roblatour/ESP32TimeServer/main/main.cpp

// ESP32 Time Server v3.0.4
// Copyright Rob Latour, 2026
// License: MIT
// Website: https://github.com/roblatour/ESP32TimeServer
//
// ESP32 Dev Board:     ESP32-P4-ETH https://www.waveshare.com/esp32-p4-eth.htm
//                                   https://www.waveshare.com/wiki/ESP32-P4-ETH?srsltid=AfmBOoo6nZm5hsPAhtpzT6lWSHd2zhWNPM_mqgbNvyoESbjvbO7uykcH
//
//                      NOTE: Powering a Waveshare ESP32-P4 POE development board by either a USB C cable or
//                      via POE Ethernet cable is sufficient to power this project,
//
//                      *****************************************************************************************************
//                      * HOWEVER DO NOT POWER THE DEVELOPMENT BOARD VIA BOTH ITS USB C CONNECTION AND POE AT THE SAME TIME *
//                      *****************************************************************************************************
//
// GNSS (recommended):  SparkFun GNSS Receiver Breakout - MAX-M10S  https://www.sparkfun.com/sparkfun-gnss-receiver-breakout-max-m10s-qwiic.html
//
// LCD2004:             blue/green screen with HD44780 I2C serial interface adapter https://www.aliexpress.com/item/1005006829045609.html.
//
// Wiring:
//
// (mandatory) GNSS module wiring to and from the ESP32-P4-ETH board:
// GNSS GND            <- -> ESP32-P4-ETH GND
// GNSS VCC            <- -> ESP32-P4-ETH 3V3
// GNSS TXD            <- -> ESP32-P4-ETH GPIO17 (RX)
// GNSS RXD            <- -> ESP32-P4-ETH GPIO16 (TX)
// GNSS PPS            <- -> ESP32-P4-ETH GPIO18
//
// (optional) LCD204A V1.5 (HD44780 + PCF8574T I2C backpack) wiring to and from the ESP32-P4-ETH board:
// LCD GND            <- -> ESP32-P4-ETH GND
// LCD VCC            <- -> ESP32-P4-ETH 3V3
// LCD SDA            <- -> ESP32-P4-ETH GPIO8 (SDA)
// LCD SLC/SCL        <- -> ESP32-P4-ETH GPIO7 (SCL)
//
// (optional) Uptime momentary button to and from teh ESP32-P4-ETH board:
// one terminal       <- -> ESP32-P4-ETH GPI03
// the other terminal <- -> ESP32-P4-ETH GND

#include <atomic>
#include <cerrno>
#include <cstdarg>
#include <cstdio>
#include <cstdlib>
#include <cstring>
#include <ctime>
#include <dirent.h>
#include <sys/stat.h>
#include <sys/time.h>
#include <unistd.h>
#include <algorithm>
#include <string>
#include <vector>

#include "Arduino.h"
#include "ArduinoOTA.h"
#include "ETH.h"
#include "SparkFun_u-blox_GNSS_v3.h"
#include "ESP32TimeServerSettings.h"
#include "custom/app_metadata.h"
#if SYMMETRIC_KEY_AUTHENTICATION_ENABLED
#include "custom/ntp_auth.h"
#endif
#include "custom/ntp_cache.h"

extern "C"
{
#include "esp_chip_info.h"
#include "esp_event.h"
#include "esp_eth_clock.h"
#include "esp_eth_driver.h"
#include "esp_eth_mac_esp.h"
#include "esp_log.h"
#include "ff.h"
#include "esp_mac.h"
#if MQTT_ENABLED
#include "esp_heap_caps.h"
#include "mqtt_client.h"
#endif
#include "esp_netif.h"
#include "esp_rom_sys.h"
#include "esp_timer.h"
#include "esp_vfs_fat.h"
#include "nvs.h"
#include "driver/mcpwm_cap.h"
#if RBG_LED_KY_016_MODULE_ENABLED
#include "driver/ledc.h"
#endif
#if RBG_LED_WS2812_MODULE_ENABLED
#include "led_strip.h"
#endif
#include "driver/sdmmc_host.h"
#include "sd_pwr_ctrl_by_on_chip_ldo.h"
#include "sdmmc_cmd.h"
#include "nvs_flash.h"
#include "driver/gpio.h"
#include "freertos/FreeRTOS.h"
#include "freertos/event_groups.h"
#include "freertos/queue.h"
#include "freertos/semphr.h"
#include "freertos/task.h"
#if LIQUID_CRYSTAL_DISPLAY_ENABLED
#include "hd44780.h"
#include "pcf8574.h"
#endif
#include "lwip/inet.h"
#include "lwip/sockets.h"
}

static const char *TAG = "main_cpp";

// the following is used to determine the NTP load shedding threshold based on the ESP32-P4 chip version
static constexpr uint32_t NTP_Requests_Per_Second_Load_Shedding_Threshold_ESP32P4_ChipVersion1_3 = 8500;
static constexpr uint32_t NTP_Requests_Per_Second_Load_Shedding_Threshold_ESP32P4_ChipVersion_above_1_3 = 14500;
static uint32_t NTP_Requests_Per_Second_Load_Shedding_Threshold = 0;

// Optional startup health test
//
// When enabled the startup health test will perform a series of checks to ensure the system is functioning correctly at boot.
//
// These tests include:
//
// Part 1: the program sends itself NTPv3 and NTPv4 (standard and interleaved ) requests via IPv4 and IPv6,
// using loop back and assigned addresses,
//
// Part 2: it health test the same logic that all NTP requests go through to receive those requests,
// process and reply to them using standard and RFC 9769-compatible interleaved  responses,
//
// Part 3: it verifying the responses to ensure proper operations and reports a pass/fail result.
//
// Additionally, this activity is reflected in regular receive/send/client stats within MQTT reporting. .
//
// The startup health test can be useful during development and troubleshooting, but it slightly increase boot time
// and resource usage.
//
// However, it is recommended to keep this option be disabled in production builds to minimize boot time and resource usage.
// Also, and perhaps more importantly, as its results may be misinterpreted.
// For example: if the user's network does not support IPv6 the IPv6 tests may fail even though the system is
// functioning correctly.
//
// Here is what a successful startup health test looks like in the logs:
/*


I (39724) main_cpp: Health Check started
I (39725) main_cpp: Health Check 01 - IPv4 loopback: NTPv3 standard      - Passed
I (39725) main_cpp: Health Check 02 - IPv4 loopback: NTPv4 standard      - Passed
I (39731) main_cpp: Health Check 03 - IPv4 loopback: NTPv4 interleaved   - Passed
I (39739) main_cpp: Health Check 04 - IPv4 loopback: NTPv4 auth standard - Passed
I (39746) main_cpp: Health Check 05 - IPv4 loopback: NTPv4 auth interlv  - Passed
I (39753) main_cpp: Health Check 06 - IPv4 loopback: NTPv4 invalid auth  - Passed
I (39760) main_cpp: Health Check 07 - IPv4 loopback: NTPv4 unknown key   - Passed
I (39767) main_cpp: Health Check 08 - IPv4 loopback: NTPv4 truncated MAC - Passed
I (39775) main_cpp: Health Check 09 - IPv4 loopback: NTPv4 altered reply - Passed
I (39782) main_cpp: Health Check 10 - IPv4 assigned: NTPv3 standard      - Passed
I (39789) main_cpp: Health Check 11 - IPv4 assigned: NTPv4 standard      - Passed
I (39796) main_cpp: Health Check 12 - IPv4 assigned: NTPv4 interleaved   - Passed
I (39803) main_cpp: Health Check 13 - IPv4 assigned: NTPv4 auth standard - Passed
I (39811) main_cpp: Health Check 14 - IPv4 assigned: NTPv4 auth interlv  - Passed
I (39818) main_cpp: Health Check 15 - IPv4 assigned: NTPv4 invalid auth  - Passed
I (39825) main_cpp: Health Check 16 - IPv4 assigned: NTPv4 unknown key   - Passed
I (39832) main_cpp: Health Check 17 - IPv4 assigned: NTPv4 truncated MAC - Passed
I (39839) main_cpp: Health Check 18 - IPv4 assigned: NTPv4 altered reply - Passed
I (39847) main_cpp: Health Check 19 - IPv6 loopback: NTPv3 standard      - Passed
I (39854) main_cpp: Health Check 20 - IPv6 loopback: NTPv4 standard      - Passed
I (39861) main_cpp: Health Check 21 - IPv6 loopback: NTPv4 interleaved   - Passed
I (39868) main_cpp: Health Check 22 - IPv6 loopback: NTPv4 auth standard - Passed
I (39876) main_cpp: Health Check 23 - IPv6 loopback: NTPv4 auth interlv  - Passed
I (39883) main_cpp: Health Check 24 - IPv6 loopback: NTPv4 invalid auth  - Passed
I (39890) main_cpp: Health Check 25 - IPv6 loopback: NTPv4 unknown key   - Passed
I (39897) main_cpp: Health Check 26 - IPv6 loopback: NTPv4 truncated MAC - Passed
I (39904) main_cpp: Health Check 27 - IPv6 loopback: NTPv4 altered reply - Passed
I (39912) main_cpp: Health Check 28 - IPv6 assigned: NTPv3 standard      - Passed
I (39919) main_cpp: Health Check 29 - IPv6 assigned: NTPv4 standard      - Passed
I (39926) main_cpp: Health Check 30 - IPv6 assigned: NTPv4 interleaved   - Passed
I (39933) main_cpp: Health Check 31 - IPv6 assigned: NTPv4 auth standard - Passed
I (39940) main_cpp: Health Check 32 - IPv6 assigned: NTPv4 auth interlv  - Passed
I (39948) main_cpp: Health Check 33 - IPv6 assigned: NTPv4 invalid auth  - Passed
I (39955) main_cpp: Health Check 34 - IPv6 assigned: NTPv4 unknown key   - Passed
I (39962) main_cpp: Health Check 35 - IPv6 assigned: NTPv4 truncated MAC - Passed
I (39969) main_cpp: Health Check 36 - IPv6 assigned: NTPv4 altered reply - Passed
I (39976) main_cpp: Health Check 37 - MQTT metrics                       - Passed
I (39984) main_cpp: Health Check completed

Most of the health checks have fairly obvious purposes based on their names, but a couple of them,
truncated MAC and altered reply tests, may require more explanation (detailed below).

For truncated MAC:
This test sends an otherwise valid NTP packet but deliberately cuts off part of the authentication field (the Message Authentication Code)
before the server processes it. The server receives a packet whose header and timestamps look fine, but whose MAC is shorter than expected,
so when it tries to verify the MAC at the end of the packet, the check fails and the reply is rejected or flagged as invalid. In effect,
it’s testing that the server does not accept packets where the integrity/authentication data has been damaged or partially missing, even
though the rest of the packet structure appears normal.

For altered reply:
This test takes a valid NTP response and then modifies some of its contents—typically one or more timestamp fields or other critical header
values—after the server has generated it but before the client treats it as trustworthy. When the client compares the altered reply against
what it expects (e.g., matching originate/receive/transmit timestamps or internal state), the inconsistency causes the response to be rejected
or treated as an error rather than used to adjust time. By doing this, the test checks that the client detects tampering or corruption in the
reply and doesn’t blindly accept time data that has been changed in transit.

*/

#define STARTUP_HEALTH_TEST_ENABLED 0 // 0 = Disabled; 1 = Enabled

// The following conditional compile flag is used to determine the ideal stack sizes for
// xTaskCreatePinnedToCore calls used throughout the program.
//
// Unless you are changing the code associated with options below and need to know the impacts of
// those changes have on the stack sizes then the conditional compile flags below should be disabled

#define CALCULATE_STACK_SIZES_ENABLED 0 // 0 = Disabled; 1 = Enabled

// FreeRTOS task stack allocations, in bytes.

static constexpr size_t Ethernet_Transport_Recovery_Task_Stack_Size = 3072;
static constexpr size_t GNSS_Recovery_Task_Stack_Size = 12288;
static constexpr size_t GNSS_Time_Sync_Task_Stack_Size = 2517;
static constexpr size_t Hardware_NTP_Server_Task_Stack_Size = 4096;
static constexpr size_t LED_LCD_Button_Task_Stack_Size = 3217;
static constexpr size_t Ethernet_Setup_Task_Stack_Size = 4096;
static constexpr size_t MQTT_Service_Task_Stack_Size = 3512;
static constexpr size_t NTP_Cache_Purge_Task_Stack_Size = 2304;
static constexpr size_t NTP_Server_Task_Stack_Size = 3560;
static constexpr size_t OTE_Service_Task_Stack_Size = 3560; // unlikely to exceed this stack size (based on current implementation)
static constexpr size_t PPS_Discipline_Task_Stack_Size = 2390;

static constexpr unsigned int Default_Safety_Margin_Percent = 30; // unless otherwise specified add this percentage to the highest stack usage as a safety margin

#if CALCULATE_STACK_SIZES_ENABLED

// For the purposes of calculating stack sizes force DEBUG_ENABLED if any of the stack size calculations are enabled
// so that the task includes all debug processing is included in the stack size calculations
#define DEBUG_ENABLED 1

// For the purposes of calculating stack sizes force all MQTT tasks as enabled if MQTT_ENABLED is enabled
#if MQTT_ENABLED
#define MQTT_CLIENT_REPORTING_ENABLED 1
#define MQTT_MEMORY_REPORTING_ENABLED 1
#define MQTT_HISTORICAL_REPORTING_ENABLED 1
#endif

typedef enum
{
    Ethernet_Transport_Recovery,
    GNSS_Recovery,
    GNSS_Time_Sync,
    Hardware_NTP_Server,
    LED_LCD_Button,
    MQTT_Service,
    NTP_Cache_Purge,
    NTP_Server,
    OTE_Service,
    PPS_Discipline
} TaskToPinToCore_t;

static size_t Highest_Ethernet_Transport_Recovery_Task_Stack_Size = 0;
static size_t Highest_GNSS_Recovery_Task_Stack_Size = 0;
static size_t Highest_GNSS_Time_Sync_Task_Stack_Size = 0;
static size_t Highest_Hardware_NTP_Server_Task_Stack_Size = 0;
static size_t Highest_LED_LCD_Button_Task_Stack_Size = 0;
static size_t Highest_MQTT_Service_Task_Stack_Size = 0;
static size_t Highest_NTP_Cache_Purge_Task_Stack_Size = 0;
static size_t Highest_NTP_Server_Task_Stack_Size = 0;
static size_t Highest_OTE_Service_Task_Stack_Size = 0;
static size_t Highest_PPS_Discipline_Task_Stack_Size = 0;

static SemaphoreHandle_t s_task_stack_usage_mutex = nullptr;

static void report_current_task_stack_usage(TaskToPinToCore_t task_id)
{
    xSemaphoreTake(s_task_stack_usage_mutex, portMAX_DELAY);

    const char *task_name = nullptr;
    size_t allocated_bytes = 0;
    unsigned int safety_margin_percent = 30;
    bool highest_value_changed = false;
    bool show_details = false;

    switch (task_id)
    {
    case Ethernet_Transport_Recovery:
        task_name = "ethernet_transport_task";
        allocated_bytes = Ethernet_Transport_Recovery_Task_Stack_Size;
        break;
    case GNSS_Recovery:
        task_name = "gnss_recovery_task";
        allocated_bytes = GNSS_Recovery_Task_Stack_Size;
        break;
    case GNSS_Time_Sync:
        task_name = "gnss_time_sync_task";
        allocated_bytes = GNSS_Time_Sync_Task_Stack_Size;
        break;
    case Hardware_NTP_Server:
        task_name = "hardware_ntp_server_task";
        allocated_bytes = Hardware_NTP_Server_Task_Stack_Size;
        break;
    case LED_LCD_Button:
        task_name = "LED_LCD_Button_task";
        allocated_bytes = LED_LCD_Button_Task_Stack_Size;
        safety_margin_percent = 70;
        break;
    case MQTT_Service:
        task_name = "mqtt_service_task";
        allocated_bytes = MQTT_Service_Task_Stack_Size;
        break;
    case NTP_Cache_Purge:
        task_name = "ntp_cache_purge_task";
        allocated_bytes = NTP_Cache_Purge_Task_Stack_Size;
        break;
    case NTP_Server:
        task_name = "ntp_server_task";
        allocated_bytes = NTP_Server_Task_Stack_Size;
        safety_margin_percent = 50;
        break;
    case OTE_Service:
        task_name = "ote_service_task";
        allocated_bytes = OTE_Service_Task_Stack_Size;
        break;
    case PPS_Discipline:
        task_name = "pps_discipline_task";
        allocated_bytes = PPS_Discipline_Task_Stack_Size;
        break;
    default:
        task_name = "unknown_task";
        break;
    }

    // calculate the suggested stack size based on the peak usage and safety margin

    const size_t high_watermark_bytes = uxTaskGetStackHighWaterMark(nullptr);
    const size_t peak_usage_bytes = allocated_bytes > high_watermark_bytes ? allocated_bytes - high_watermark_bytes : 0;
    const size_t curent_suggestion = (peak_usage_bytes * (100U + safety_margin_percent) + 99U) / 100U;

    if (show_details)
    {
        ESP_LOGI(task_name,
                 "Stack report: Allocated=%u bytes, HighWater=%u bytes unused, PeakUsage=%u bytes, Suggested=%u bytes",
                 static_cast<unsigned int>(allocated_bytes),
                 static_cast<unsigned int>(high_watermark_bytes),
                 static_cast<unsigned int>(peak_usage_bytes),
                 static_cast<unsigned int>(curent_suggestion));
    }

    if (curent_suggestion == 0)
        ESP_LOGE(task_name, "Error: Suggested stack size is 0 bytes. Try increasing the allocted bytes of %u", static_cast<unsigned int>(allocated_bytes));

    switch (task_id)
    {
    case Ethernet_Transport_Recovery:
        if (curent_suggestion > Highest_Ethernet_Transport_Recovery_Task_Stack_Size)
        {
            Highest_Ethernet_Transport_Recovery_Task_Stack_Size = curent_suggestion;
            highest_value_changed = true;
        }
        break;
    case GNSS_Recovery:
        if (curent_suggestion > Highest_GNSS_Recovery_Task_Stack_Size)
        {
            Highest_GNSS_Recovery_Task_Stack_Size = curent_suggestion;
            highest_value_changed = true;
        }
        break;
    case GNSS_Time_Sync:
        if (curent_suggestion > Highest_GNSS_Time_Sync_Task_Stack_Size)
        {
            Highest_GNSS_Time_Sync_Task_Stack_Size = curent_suggestion;
            highest_value_changed = true;
        }
        break;
    case Hardware_NTP_Server:
        if (curent_suggestion > Highest_Hardware_NTP_Server_Task_Stack_Size)
        {
            Highest_Hardware_NTP_Server_Task_Stack_Size = curent_suggestion;
            highest_value_changed = true;
        }
        break;
    case LED_LCD_Button:
        if (curent_suggestion > Highest_LED_LCD_Button_Task_Stack_Size)
        {
            Highest_LED_LCD_Button_Task_Stack_Size = curent_suggestion;
            highest_value_changed = true;
        }
        break;
    case MQTT_Service:
        if (curent_suggestion > Highest_MQTT_Service_Task_Stack_Size)
        {
            Highest_MQTT_Service_Task_Stack_Size = curent_suggestion;
            highest_value_changed = true;
        }
        break;
    case NTP_Cache_Purge:
        if (curent_suggestion > Highest_NTP_Cache_Purge_Task_Stack_Size)
        {
            Highest_NTP_Cache_Purge_Task_Stack_Size = curent_suggestion;
            highest_value_changed = true;
        }
        break;
    case NTP_Server:
        if (curent_suggestion > Highest_NTP_Server_Task_Stack_Size)
        {
            Highest_NTP_Server_Task_Stack_Size = curent_suggestion;
            highest_value_changed = true;
        }
        break;
    case OTE_Service:
        if (curent_suggestion > Highest_OTE_Service_Task_Stack_Size)
        {
            Highest_OTE_Service_Task_Stack_Size = curent_suggestion;
            highest_value_changed = true;
        }

        break;
    case PPS_Discipline:
        if (curent_suggestion > Highest_PPS_Discipline_Task_Stack_Size)
        {
            Highest_PPS_Discipline_Task_Stack_Size = curent_suggestion;
            highest_value_changed = true;
        }
        break;
    default:

        break;
    }

    // Report the highest suggested stack sizes for all tasks to date in such a way that they can be easily copied into the code above
    // If no new highest value has yet been reported for a task the value shown will be 0, the old value will remain as the comment
    if (highest_value_changed)
    {
        ESP_LOGI(TAG, "Suggested updated task stack sizes:");
        ESP_LOGI(TAG, " ");

        if (Highest_Ethernet_Transport_Recovery_Task_Stack_Size > Ethernet_Transport_Recovery_Task_Stack_Size)
            ESP_LOGW(TAG, "static constexpr size_t Ethernet_Transport_Recovery_Task_Stack_Size = %u; // %u;", static_cast<unsigned int>(Highest_Ethernet_Transport_Recovery_Task_Stack_Size), static_cast<unsigned int>(Ethernet_Transport_Recovery_Task_Stack_Size));
        else
            ESP_LOGI(TAG, "static constexpr size_t Ethernet_Transport_Recovery_Task_Stack_Size = %u; // %u;", static_cast<unsigned int>(Highest_Ethernet_Transport_Recovery_Task_Stack_Size), static_cast<unsigned int>(Ethernet_Transport_Recovery_Task_Stack_Size));

        if (Highest_GNSS_Recovery_Task_Stack_Size > GNSS_Recovery_Task_Stack_Size)
            ESP_LOGW(TAG, "static constexpr size_t GNSS_Recovery_Task_Stack_Size = %u; // %u;", static_cast<unsigned int>(Highest_GNSS_Recovery_Task_Stack_Size), static_cast<unsigned int>(GNSS_Recovery_Task_Stack_Size));
        else
            ESP_LOGI(TAG, "static constexpr size_t GNSS_Recovery_Task_Stack_Size = %u; // %u;", static_cast<unsigned int>(Highest_GNSS_Recovery_Task_Stack_Size), static_cast<unsigned int>(GNSS_Recovery_Task_Stack_Size));

        if (Highest_GNSS_Time_Sync_Task_Stack_Size > GNSS_Time_Sync_Task_Stack_Size)
            ESP_LOGW(TAG, "static constexpr size_t GNSS_Time_Sync_Task_Stack_Size = %u; // %u;", static_cast<unsigned int>(Highest_GNSS_Time_Sync_Task_Stack_Size), static_cast<unsigned int>(GNSS_Time_Sync_Task_Stack_Size));
        else
            ESP_LOGI(TAG, "static constexpr size_t GNSS_Time_Sync_Task_Stack_Size = %u; // %u;", static_cast<unsigned int>(Highest_GNSS_Time_Sync_Task_Stack_Size), static_cast<unsigned int>(GNSS_Time_Sync_Task_Stack_Size));

        if (Highest_Hardware_NTP_Server_Task_Stack_Size > Hardware_NTP_Server_Task_Stack_Size)
            ESP_LOGW(TAG, "static constexpr size_t Hardware_NTP_Server_Task_Stack_Size = %u; // %u;", static_cast<unsigned int>(Highest_Hardware_NTP_Server_Task_Stack_Size), static_cast<unsigned int>(Hardware_NTP_Server_Task_Stack_Size));
        else
            ESP_LOGI(TAG, "static constexpr size_t Hardware_NTP_Server_Task_Stack_Size = %u; // %u;", static_cast<unsigned int>(Highest_Hardware_NTP_Server_Task_Stack_Size), static_cast<unsigned int>(Hardware_NTP_Server_Task_Stack_Size));

        if (Highest_LED_LCD_Button_Task_Stack_Size > LED_LCD_Button_Task_Stack_Size)
            ESP_LOGW(TAG, "static constexpr size_t LED_LCD_Button_Task_Stack_Size = %u; // %u;", static_cast<unsigned int>(Highest_LED_LCD_Button_Task_Stack_Size), static_cast<unsigned int>(LED_LCD_Button_Task_Stack_Size));
        else
            ESP_LOGI(TAG, "static constexpr size_t LED_LCD_Button_Task_Stack_Size = %u; // %u;", static_cast<unsigned int>(Highest_LED_LCD_Button_Task_Stack_Size), static_cast<unsigned int>(LED_LCD_Button_Task_Stack_Size));

        if (Highest_MQTT_Service_Task_Stack_Size > MQTT_Service_Task_Stack_Size)
            ESP_LOGW(TAG, "static constexpr size_t MQTT_Service_Task_Stack_Size = %u; // %u;", static_cast<unsigned int>(Highest_MQTT_Service_Task_Stack_Size), static_cast<unsigned int>(MQTT_Service_Task_Stack_Size));
        else
            ESP_LOGI(TAG, "static constexpr size_t MQTT_Service_Task_Stack_Size = %u; // %u;", static_cast<unsigned int>(Highest_MQTT_Service_Task_Stack_Size), static_cast<unsigned int>(MQTT_Service_Task_Stack_Size));

        if (Highest_NTP_Cache_Purge_Task_Stack_Size > NTP_Cache_Purge_Task_Stack_Size)
            ESP_LOGW(TAG, "static constexpr size_t NTP_Cache_Purge_Task_Stack_Size = %u; // %u;", static_cast<unsigned int>(Highest_NTP_Cache_Purge_Task_Stack_Size), static_cast<unsigned int>(NTP_Cache_Purge_Task_Stack_Size));
        else
            ESP_LOGI(TAG, "static constexpr size_t NTP_Cache_Purge_Task_Stack_Size = %u; // %u;", static_cast<unsigned int>(Highest_NTP_Cache_Purge_Task_Stack_Size), static_cast<unsigned int>(NTP_Cache_Purge_Task_Stack_Size));

        if (Highest_NTP_Server_Task_Stack_Size > NTP_Server_Task_Stack_Size)
            ESP_LOGW(TAG, "static constexpr size_t NTP_Server_Task_Stack_Size = %u; // %u;", static_cast<unsigned int>(Highest_NTP_Server_Task_Stack_Size), static_cast<unsigned int>(NTP_Server_Task_Stack_Size));
        else
            ESP_LOGI(TAG, "static constexpr size_t NTP_Server_Task_Stack_Size = %u; // %u;", static_cast<unsigned int>(Highest_NTP_Server_Task_Stack_Size), static_cast<unsigned int>(NTP_Server_Task_Stack_Size));

        if (Highest_OTE_Service_Task_Stack_Size > OTE_Service_Task_Stack_Size)
            ESP_LOGW(TAG, "static constexpr size_t OTE_Service_Task_Stack_Size = %u; // %u;", static_cast<unsigned int>(Highest_OTE_Service_Task_Stack_Size), static_cast<unsigned int>(OTE_Service_Task_Stack_Size));
        else
            ESP_LOGI(TAG, "static constexpr size_t OTE_Service_Task_Stack_Size = %u; // %u;", static_cast<unsigned int>(Highest_OTE_Service_Task_Stack_Size), static_cast<unsigned int>(OTE_Service_Task_Stack_Size));

        if (Highest_PPS_Discipline_Task_Stack_Size > PPS_Discipline_Task_Stack_Size)
            ESP_LOGW(TAG, "static constexpr size_t PPS_Discipline_Task_Stack_Size = %u; // %u;", static_cast<unsigned int>(Highest_PPS_Discipline_Task_Stack_Size), static_cast<unsigned int>(PPS_Discipline_Task_Stack_Size));
        else
            ESP_LOGI(TAG, "static constexpr size_t PPS_Discipline_Task_Stack_Size = %u; // %u;", static_cast<unsigned int>(Highest_PPS_Discipline_Task_Stack_Size), static_cast<unsigned int>(PPS_Discipline_Task_Stack_Size));

        ESP_LOGI(TAG, " ");
    };

    xSemaphoreGive(s_task_stack_usage_mutex);
}

#endif

#ifndef UBLOX_COMPLIANT_GNSS_RECEIVER_ENABLED
#define UBLOX_COMPLIANT_GNSS_RECEIVER_ENABLED 1
#endif

static constexpr gpio_num_t ETH_MDC_GPIO = GPIO_NUM_31;
static constexpr gpio_num_t ETH_MDIO_GPIO = GPIO_NUM_52;
static constexpr gpio_num_t ETH_PHY_RST_GPIO = GPIO_NUM_51;
static constexpr int ETH_PHY_ADDRESS = 1;

#if LIQUID_CRYSTAL_DISPLAY_ENABLED
static constexpr i2c_port_t LCD_I2C_PORT = I2C_NUM_0;
static constexpr gpio_num_t LCD_I2C_SDA_GPIO = GPIO_NUM_8;
static constexpr gpio_num_t LCD_I2C_SCL_GPIO = GPIO_NUM_7;
#endif

static constexpr uint16_t NTP_PORT = 123;
static constexpr size_t NTP_PACKET_SIZE = 48;
#if SYMMETRIC_KEY_AUTHENTICATION_ENABLED
static constexpr size_t NTP_MAX_PACKET_SIZE = NTP_PACKET_SIZE + NTP_AUTH_TRAILER_SIZE;
#else
static constexpr size_t NTP_MAX_PACKET_SIZE = NTP_PACKET_SIZE;
#endif
static constexpr uint64_t NTP_EPOCH_OFFSET = 2208988800ULL;
static constexpr int8_t NTP_PRECISION_EXPONENT = -13;
static constexpr uint32_t NTP_ROOT_DISPERSION = 66;
static constexpr uint64_t NTP_CACHE_TIMESTAMP_MATCH_TOLERANCE = 8;
static constexpr size_t NTP_SOCKET_BATCH_LIMIT = 16;
static constexpr EventBits_t ETH_CONNECTED_BIT = BIT0;
static constexpr EventBits_t ETH_GOT_IP_BIT = BIT1;
static constexpr EventBits_t ETH_GOT_IP6_BIT = BIT2;
static constexpr EventBits_t ETH_GOT_ROUTABLE_IP6_BIT = BIT3;
static constexpr size_t IP_ADDRESS_TEXT_SIZE = INET6_ADDRSTRLEN;
static constexpr uint32_t ROUTABLE_IPV6_ACQUISITION_TIMEOUT_MS = 30000;
static constexpr uint32_t OTE_Failure_Display_Time_Ms = 10000;
static constexpr uint32_t OTE_Reboot_Delay_Ms = 5000;

#if LIQUID_CRYSTAL_DISPLAY_ENABLED
static i2c_dev_t s_lcd_io{};
static uint8_t s_lcd_addr = 0;
static bool s_lcd_ready = false;
static hd44780_t s_lcd{};
static char s_lcd_last_lines[lcdRows][lcdColumns + 1] = {};
static bool s_lcd_line_cached[lcdRows] = {};
#else
#define display_line(...)
#endif

static std::string MACToBeUsed;

struct PpsCaptureEvent
{
    int64_t approximate_edge_us;
};

static constexpr uint32_t PPS_CAPTURE_RESOLUTION_HZ = 80000000;

static EventGroupHandle_t s_net_event_group = nullptr;
static SemaphoreHandle_t s_network_address_mutex = nullptr;
static SemaphoreHandle_t s_time_mutex = nullptr;
static SemaphoreHandle_t s_pps_semaphore = nullptr;
static QueueHandle_t s_pps_timestamp_queue = nullptr;
static QueueHandle_t s_pps_sync_timestamp_queue = nullptr;
static mcpwm_cap_timer_handle_t s_pps_capture_timer = nullptr;
static mcpwm_cap_channel_handle_t s_pps_capture_channel = nullptr;
static SemaphoreHandle_t s_ote_mutex = nullptr;
#if LIQUID_CRYSTAL_DISPLAY_ENABLED
static SemaphoreHandle_t s_lcd_mutex = nullptr;
#endif
static SemaphoreHandle_t s_sync_state_mutex = nullptr;

#if OTE_UPDATES_ENABLED
static bool s_ote_in_progress = false;
static bool s_ote_failed = false;
static bool s_ote_success = false;
static int s_ote_progress_percent = -1;
static int64_t s_ote_failure_display_until_us = 0;
static int64_t s_ote_reboot_at_us = 0;
static char s_ote_error_reason[lcdColumns + 1] = "";
#endif

static std::atomic<bool> s_safe_guard_tripped{false};
static std::atomic<bool> s_time_setting_in_progress{false};
static std::atomic<bool> s_time_has_been_set{false};
static std::atomic<uint64_t> s_ntp_reference_time_64{0};
static std::atomic<bool> s_ntp_reference_valid{false};
static std::atomic<bool> s_ptp_clock_ready{false};

static_assert(PreferIPvX == 0 || PreferIPvX == 1 || PreferIPvX == 2 || PreferIPvX == 4 || PreferIPvX == 6 || PreferIPvX == 8 || PreferIPvX == 9,
              "PreferIPvX must be 0, 1, 2, 4, 6, 8, or 9");

static char s_ip_address[IP_ADDRESS_TEXT_SIZE] = "";
static char s_ipv4_address[INET_ADDRSTRLEN] = "";
static char s_ipv6_address[IP_ADDRESS_TEXT_SIZE] = "";
enum class ipv6_address_priority_t : uint8_t
{
    none,
    link_local,
    unique_local,
    global_unicast
};
static ipv6_address_priority_t s_ipv6_address_priority = ipv6_address_priority_t::none;

struct network_address_snapshot_t
{
    char selected[IP_ADDRESS_TEXT_SIZE];
    char ipv4[INET_ADDRSTRLEN];
    char ipv6[IP_ADDRESS_TEXT_SIZE];
    ipv6_address_priority_t ipv6_priority;
};

static constexpr bool IPV4_ENABLED = PreferIPvX != 2;
static constexpr bool IPV6_ENABLED = PreferIPvX != 1;

static bool has_usable_network_address(EventBits_t event_bits)
{
    if (PreferIPvX == 1)
        return (event_bits & ETH_GOT_IP_BIT) != 0;
    if (PreferIPvX == 2)
        return (event_bits & ETH_GOT_ROUTABLE_IP6_BIT) != 0;
    return (event_bits & (ETH_GOT_IP_BIT | ETH_GOT_ROUTABLE_IP6_BIT)) != 0;
}

static void update_selected_ip_address_locked()
{
    const bool has_ipv4 = s_ipv4_address[0] != '\0';
    const bool has_ipv6 = s_ipv6_address[0] != '\0';

    const char *selected_address = "";
    if (PreferIPvX == 1)
        selected_address = s_ipv4_address;
    else if (PreferIPvX == 2)
        selected_address = s_ipv6_address;
    else if (PreferIPvX == 4)
        selected_address = has_ipv4 ? s_ipv4_address : s_ipv6_address;
    else if (PreferIPvX == 6)
        selected_address = has_ipv6 ? s_ipv6_address : s_ipv4_address;
    else if (strcmp(s_ip_address, s_ipv4_address) == 0 && has_ipv4)
        selected_address = s_ipv4_address;
    else if (strcmp(s_ip_address, s_ipv6_address) == 0 && has_ipv6)
        selected_address = s_ipv6_address;
    else
        selected_address = has_ipv4 ? s_ipv4_address : s_ipv6_address;

    snprintf(s_ip_address, sizeof(s_ip_address), "%s", selected_address);
}

static network_address_snapshot_t get_network_address_snapshot()
{
    network_address_snapshot_t snapshot{};
    if (s_network_address_mutex != nullptr && xSemaphoreTake(s_network_address_mutex, portMAX_DELAY) == pdTRUE)
    {
        snprintf(snapshot.selected, sizeof(snapshot.selected), "%s", s_ip_address);
        snprintf(snapshot.ipv4, sizeof(snapshot.ipv4), "%s", s_ipv4_address);
        snprintf(snapshot.ipv6, sizeof(snapshot.ipv6), "%s", s_ipv6_address);
        snapshot.ipv6_priority = s_ipv6_address_priority;
        xSemaphoreGive(s_network_address_mutex);
    }
    return snapshot;
}

static void clear_network_addresses()
{
    if (s_network_address_mutex == nullptr || xSemaphoreTake(s_network_address_mutex, portMAX_DELAY) != pdTRUE)
        return;

    s_ip_address[0] = '\0';
    s_ipv4_address[0] = '\0';
    s_ipv6_address[0] = '\0';
    s_ipv6_address_priority = ipv6_address_priority_t::none;
    xSemaphoreGive(s_network_address_mutex);
}

static void set_network_ipv4_address(const esp_ip4_addr_t &address)
{
    if (s_network_address_mutex == nullptr || xSemaphoreTake(s_network_address_mutex, portMAX_DELAY) != pdTRUE)
        return;

    snprintf(s_ipv4_address, sizeof(s_ipv4_address), IPSTR, IP2STR(&address));
    update_selected_ip_address_locked();
    xSemaphoreGive(s_network_address_mutex);
}

static void clear_network_ipv4_address()
{
    if (s_network_address_mutex == nullptr || xSemaphoreTake(s_network_address_mutex, portMAX_DELAY) != pdTRUE)
        return;

    s_ipv4_address[0] = '\0';
    update_selected_ip_address_locked();
    xSemaphoreGive(s_network_address_mutex);
}

static ipv6_address_priority_t get_ipv6_address_priority(const struct in6_addr &address)
{
    if ((address.s6_addr[0] & 0xE0) == 0x20)
        return ipv6_address_priority_t::global_unicast;
    if ((address.s6_addr[0] & 0xFE) == 0xFC)
        return ipv6_address_priority_t::unique_local;
    return ipv6_address_priority_t::link_local;
}

static bool set_network_ipv6_address(const esp_ip6_addr_t &address)
{
    struct in6_addr parsed_address{};
    memcpy(&parsed_address, address.addr, sizeof(parsed_address));
    const ipv6_address_priority_t priority = get_ipv6_address_priority(parsed_address);
    const bool is_routable = priority >= ipv6_address_priority_t::unique_local;

    char text_address[IP_ADDRESS_TEXT_SIZE] = "";
    if (inet_ntop(AF_INET6, &parsed_address, text_address, sizeof(text_address)) == nullptr)
        return false;

    if (s_network_address_mutex == nullptr || xSemaphoreTake(s_network_address_mutex, portMAX_DELAY) != pdTRUE)
        return false;

    if (priority >= s_ipv6_address_priority)
    {
        snprintf(s_ipv6_address, sizeof(s_ipv6_address), "%s", text_address);
        s_ipv6_address_priority = priority;
        update_selected_ip_address_locked();
    }
    xSemaphoreGive(s_network_address_mutex);
    return is_routable;
}

static void refresh_network_ipv6_addresses()
{
    if (!IPV6_ENABLED || ETH.netif() == nullptr)
        return;

    esp_ip6_addr_t addresses[CONFIG_LWIP_IPV6_NUM_ADDRESSES]{};
    const int address_count = esp_netif_get_all_ip6(ETH.netif(), addresses);
    bool routable_address_acquired = false;
    for (int index = 0; index < address_count; ++index)
        routable_address_acquired = set_network_ipv6_address(addresses[index]) || routable_address_acquired;

    if (address_count > 0)
        xEventGroupSetBits(s_net_event_group, ETH_GOT_IP6_BIT);
    if (routable_address_acquired)
        xEventGroupSetBits(s_net_event_group, ETH_GOT_ROUTABLE_IP6_BIT);
}

static void log_network_ipv6_addresses()
{
    if (!IPV6_ENABLED || ETH.netif() == nullptr)
        return;

    esp_ip6_addr_t addresses[CONFIG_LWIP_IPV6_NUM_ADDRESSES]{};
    const int address_count = esp_netif_get_all_ip6(ETH.netif(), addresses);
    if (address_count == 0)
    {
        ESP_LOGW(TAG, "Ethernet IPv6 candidates: none");
        return;
    }

    for (int index = 0; index < address_count; ++index)
    {
        struct in6_addr address{};
        memcpy(&address, addresses[index].addr, sizeof(address));
        char text_address[IP_ADDRESS_TEXT_SIZE] = "";
        if (inet_ntop(AF_INET6, &address, text_address, sizeof(text_address)) == nullptr)
            continue;

        const char *type = "link-local";
        switch (get_ipv6_address_priority(address))
        {
        case ipv6_address_priority_t::global_unicast:
            type = "global-unicast";
            break;
        case ipv6_address_priority_t::unique_local:
            type = "unique-local";
            break;
        default:
            break;
        }
        ESP_LOGI(TAG, "Ethernet IPv6 candidate: %s (%s)", text_address, type);
    }
}

static std::atomic<bool> s_ethernet_connected{false};
static std::atomic<bool> s_ipv4_ever_acquired{false};
static std::atomic<int64_t> s_last_physical_link_down_us{0};
static std::atomic<bool> s_ethernet_recovery_in_progress{false};
static std::atomic<bool> s_ethernet_recovery_rx_probe_active{false};
static std::atomic<uint32_t> s_ethernet_recovery_rx_probe_frames{0};
static std::atomic<bool> s_hardware_ntp_accepting{false};
static std::atomic<bool> s_ntp_external_responses_enabled{false};
static std::atomic<bool> s_ntp_server_ready{false};
#if RBG_LED_KY_016_MODULE_ENABLED || RBG_LED_WS2812_MODULE_ENABLED
static std::atomic<bool> s_gnss_pps_startup_qualification_in_progress{false};
static void control_RGB_LED(RGB_LED_Colour Colour, bool enabled);
#endif
#if RBG_LED_WS2812_MODULE_ENABLED
static led_strip_handle_t s_ws2812_strip = nullptr;
static uint8_t s_ws2812_brightness = 0;
#endif
static std::atomic<bool> s_open_for_business_message_written{false};
static std::atomic<int64_t> s_last_hardware_ntp_response_us{0};
static std::atomic<int64_t> s_last_ntp_input_us{0};
static std::atomic<int64_t> s_first_ntp_input_us{0};
static std::atomic<int64_t> s_last_ntp_response_us{0};
static std::atomic<int64_t> s_last_load_shedding_us{0};
static std::atomic<uint64_t> s_ntp_admission_window{0};
static std::atomic<uint32_t> s_ntp_input_count{0};
static std::atomic<bool> s_ntp_shed_during_period{false};
static SemaphoreHandle_t s_hardware_ntp_transmit_mutex = nullptr;

enum class ntp_transport_health_t : uint8_t
{
    link_down,
    no_ip,
    idle,
    healthy,
    stalled
};
static std::atomic<ntp_transport_health_t> s_ntp_transport_health{ntp_transport_health_t::idle};

static bool ntp_load_shedding_active()
{
    const int64_t last_shedding_us = s_last_load_shedding_us.load(std::memory_order_relaxed);
    return last_shedding_us > 0 && esp_timer_get_time() - last_shedding_us < 1500000LL;
}

static void record_ntp_input(int64_t now_us)
{
    s_ntp_input_count.fetch_add(1, std::memory_order_relaxed);
    s_last_ntp_input_us.store(now_us, std::memory_order_relaxed);
    int64_t first_input_us = 0;
    s_first_ntp_input_us.compare_exchange_strong(first_input_us, now_us, std::memory_order_relaxed);
}

static bool admit_ntp_request()
{
    const int64_t now_us = esp_timer_get_time();
    record_ntp_input(now_us);

    const uint32_t window = static_cast<uint32_t>(now_us / 100000LL);
    const uint32_t window_limit = NTP_Requests_Per_Second_Load_Shedding_Threshold / 10;
    uint64_t current = s_ntp_admission_window.load(std::memory_order_relaxed);
    for (;;)
    {
        const uint32_t current_window = static_cast<uint32_t>(current >> 32);
        const uint32_t active_window = current_window > window ? current_window : window;
        const uint32_t count = static_cast<uint32_t>(current);
        const uint32_t next_count = current_window == active_window ? count + 1 : 1;
        if (next_count > window_limit)
        {
            s_ntp_shed_during_period.store(true, std::memory_order_relaxed);
            s_last_load_shedding_us.store(now_us, std::memory_order_relaxed);
            return false;
        }
        const uint64_t next = (static_cast<uint64_t>(active_window) << 32) | next_count;
        if (s_ntp_admission_window.compare_exchange_weak(current, next, std::memory_order_relaxed))
            return true;
    }
}

static bool configure_static_ip();
static bool configure_hardware_timestamps();
static bool start_ethernet_driver();

static bool format_socket_address(const struct sockaddr_storage &address, char *buffer, size_t buffer_size)
{
    if (buffer_size == 0)
        return false;

    const void *source = nullptr;
    if (address.ss_family == AF_INET)
        source = &reinterpret_cast<const struct sockaddr_in *>(&address)->sin_addr;
    else if (address.ss_family == AF_INET6)
        source = &reinterpret_cast<const struct sockaddr_in6 *>(&address)->sin6_addr;
    else
    {
        buffer[0] = '\0';
        return false;
    }

    return inet_ntop(address.ss_family, source, buffer, buffer_size) != nullptr;
}

#if MQTT_ENABLED

static constexpr uint32_t MQTTFrequencyOfKeepAliveRequest = 30; // in seconds (do not raise above 30

// MQTT_MAX_REPORT_SIZE is based on MQTT_TF_Client_Limit (in ESP32TimeServerSetting.h)
// please see the spreadsheet at tools/json_message_calculator.xlsx for calculation details
// Note: increasing this limit will increase memory usage for MQTT report buffering and may impact system performance.
static constexpr size_t MQTT_MAX_REPORT_SIZE = 39166;

// MQTT_REPORT_SIZE based on MQTT_CLIENT_SIZE (below)
// please see the spreadsheet at tools/json_message_calculator.xlsx for calculation details
// Note: increasing this limit will increase memory usage for MQTT report buffering and may impact system performance.
static constexpr size_t MQTT_CLIENT_LIMIT = 50;
static constexpr size_t MQTT_REPORT_SIZE = 4966;

static constexpr size_t MQTT_NTP_EVENT_QUEUE_DEPTH = 1024;
static constexpr size_t MQTT_REPORT_QUEUE_DEPTH = 4;
static constexpr size_t MQTT_NTP_EVENT_BATCH_LIMIT = 128;

static constexpr uint32_t MQTT_RESTART_PUBLISH_TIMEOUT_MS = 1000;
static constexpr uint32_t MQTT_QUEUED_PUBLISH_DELAY_MS = 250;
static constexpr char TF_MOUNT_POINT[] = "/tfcard";
static constexpr char TF_QUEUE_DIRECTORY[] = "/tfcard/Queue";

struct mqtt_client_request_t
{
    sa_family_t address_family = AF_UNSPEC;
    uint8_t address[sizeof(struct in6_addr)] = {};
    uint32_t requests = 0;
};

struct mqtt_report_t
{
    char payload[MQTT_REPORT_SIZE] = "";
};

static SemaphoreHandle_t s_mqtt_stats_mutex = nullptr;
static QueueHandle_t s_mqtt_ntp_event_queue = nullptr;
static esp_mqtt_client_handle_t s_mqtt_client = nullptr;
static std::atomic<bool> s_mqtt_setup_failed{false};
static std::atomic<bool> s_mqtt_connected{false};
static std::atomic<bool> s_mqtt_has_connected{false};
static std::atomic<int64_t> s_mqtt_disconnected_since_us{0};
static std::atomic<int> s_mqtt_restart_publish_id{-1};
static std::atomic<bool> s_mqtt_restart_publish_completed{false};
static std::atomic<uint32_t> s_pps_pulses{0};
static std::atomic<uint32_t> s_ntp_requests_this_second{0};
static std::atomic<uint32_t> s_ntp_valid_requests{0};
static std::atomic<uint32_t> s_ntp_invalid_requests{0};
static std::atomic<uint32_t> s_ntp_authenticated_valid_requests{0};
static std::atomic<uint32_t> s_ntp_authenticated_invalid_requests{0};
static std::atomic<uint32_t> s_ntp_unauthenticated_valid_requests{0};
static std::atomic<uint32_t> s_ntp_unauthenticated_invalid_requests{0};
static std::atomic<uint32_t> s_ntp_responses{0};
static std::atomic<uint32_t> s_ntp_responses_synchronized_and_disciplined{0};
static std::atomic<uint32_t> s_ntp_responses_gnss_unsynchronized{0};
static std::atomic<uint32_t> s_ntp_responses_pps_undisciplined{0};
static std::atomic<uint32_t> s_ntp_telemetry_events_dropped{0};
static std::atomic<uint8_t> s_satellite_count{0};
static std::atomic<uint8_t> s_satellite_min{UINT8_MAX};
static std::atomic<uint8_t> s_satellite_max{0};

static void mqtt_note_satellite_count(uint8_t satellites)
{
    s_satellite_count.store(satellites, std::memory_order_relaxed);

    uint8_t minimum = s_satellite_min.load(std::memory_order_relaxed);
    while (satellites < minimum &&
           !s_satellite_min.compare_exchange_weak(minimum, satellites, std::memory_order_relaxed, std::memory_order_relaxed))
    {
    }

    uint8_t maximum = s_satellite_max.load(std::memory_order_relaxed);
    while (satellites > maximum &&
           !s_satellite_max.compare_exchange_weak(maximum, satellites, std::memory_order_relaxed, std::memory_order_relaxed))
    {
    }
}

static std::atomic<int64_t> s_eth_link_connected_us{0};
static std::atomic<int64_t> s_eth_link_up_total_us{0};
#if MQTT_ENABLED && MQTT_HISTORICAL_REPORTING_ENABLED
static std::atomic<time_t> s_last_synchronized_and_disciplined{0};
static std::atomic<time_t> s_last_gnss_unsynchronized{0};
static std::atomic<time_t> s_last_pps_undisciplined{0};
static std::atomic<bool> s_historical_gnss_fault_active{false};
static std::atomic<bool> s_historical_pps_fault_active{false};
#endif

#if MQTT_ENABLED && MQTT_CLIENT_REPORTING_ENABLED
static std::atomic<bool> s_mqtt_client_table_overflown{false};
static size_t s_mqtt_client_count = 0;
#endif

static int64_t s_mqtt_last_link_up_us = 0;
static mqtt_report_t s_mqtt_reports[MQTT_REPORT_QUEUE_DEPTH]{};
static char s_mqtt_payload[MQTT_MAX_REPORT_SIZE] = "";
static char s_mqtt_final_payload[MQTT_REPORT_SIZE] = "";
static size_t s_mqtt_report_head = 0;
static std::atomic<size_t> s_mqtt_queued_messages_count{0};
static uint32_t s_mqtt_queued_messages_discarded = 0;
static mqtt_client_request_t s_mqtt_clients[MQTT_TF_Client_Limit]{};
static std::atomic<bool> s_tf_queue_available{false};
static sdmmc_card_t *s_tf_card = nullptr;
static uint64_t s_tf_queue_next_sequence = 0;
static std::atomic<uint32_t> s_ntp_most_requests_per_second{0};
static char s_mqtt_uri[64] = "";
static char s_mqtt_report_topic[128] = "";
static char s_mqtt_status_topic[128] = "";

static void mqtt_publish_final_report();
static void mqtt_enqueue_ntp_request(const struct sockaddr_storage &source_address);
#endif

static void controlled_restart(const char *reason);

static HardwareSerial s_gnss_serial(1);
static SFE_UBLOX_GNSS_SERIAL s_gnss;
static uint32_t s_detected_gnss_baud = 0;
static std::atomic<bool> s_saved_gnss_baud_communication_failed{false};
static bool s_gnss_required_assume_success = false;

// The following flag for National Marine Electronics Association (NEMA) fallback doesn't determine if it is allowed or not
// rather the program sets it to true if it is required (due to an older / ubox noncompliant hardware gnss module being used)

static bool s_use_nmea_fallback = false;
static bool s_gnss_is_max_m10s = false;
static std::atomic<bool> s_gnss_locked{false};
static std::atomic<int64_t> s_gnss_lock_started_us{0};
static std::atomic<int64_t> s_gnss_locked_total_us{0};
static std::atomic<bool> s_pps_discipline_active{false};
static std::atomic<bool> s_gnss_recovery_in_progress{false};
static std::atomic<int64_t> s_last_gnss_recovery_us{0};

struct sync_faults_t
{
    bool pps_missing = false;
    bool gnss_invalid = false;
    bool sanity_mismatch = false;
    bool sync_stale = false;
};

static bool has_sync_fault(const sync_faults_t &faults)
{
    return faults.pps_missing || faults.gnss_invalid || faults.sanity_mismatch || faults.sync_stale;
}

struct sync_state_t
{
    int64_t last_successful_sync_us = 0;
    int64_t last_sync_attempt_us = 0;
    int64_t last_pps_seen_us = 0;
    time_t last_sync_delta_seconds = 0;
    uint32_t consecutive_sync_failures = 0;
    uint32_t consecutive_sanity_failures = 0;
    bool holdover_mode = false;
    bool pps_active = false;
    bool gnss_timing_valid = false;
    int64_t last_gnss_valid_us = 0;
    sync_faults_t faults{};
};

struct sync_candidate_t
{
    time_t candidate_time = 0;
    bool use_pps_alignment = false;
    bool used_nmea_fallback = false;
    int64_t pps_release_time_us = 0;
    sync_faults_t failures{};
};

static sync_state_t s_sync_state{};
static sync_state_t get_sync_state_snapshot();
static std::atomic<uint32_t> s_ntp_sync_state_sequence{0};
static std::atomic<int64_t> s_ntp_last_successful_sync_us{0};
static std::atomic<int64_t> s_ntp_last_gnss_valid_us{0};
static std::atomic<bool> s_ntp_pps_active{false};
static std::atomic<bool> s_ntp_gnss_timing_valid{false};
static std::atomic<bool> s_ntp_pps_missing{false};
static std::atomic<bool> s_ntp_gnss_invalid{false};
static std::atomic<bool> s_ntp_sanity_mismatch{false};
static std::atomic<bool> s_ntp_sync_stale{false};
static constexpr int64_t Sync_Stale_After_Us = static_cast<int64_t>(periodicGNSSRefreshEveryThisNumberOfMinutes) * 60LL * 1000000LL * 3LL;
static constexpr int64_t Gnss_Validity_Timeout_Us = 3500000LL;
static constexpr int64_t Sync_Reboot_After_Us = 30LL * 60LL * 1000000LL;
static constexpr int64_t Max_Sync_Attempt_Us = 10000000LL;
static constexpr int64_t Gnss_Invalid_Reacquisition_After_Us = 30LL * 1000000LL;
static constexpr int64_t Runtime_gnss_Recovery_Min_Interval_Us = 5LL * 60LL * 1000000LL;
static constexpr uint32_t Sync_Failures_Before_Runtime_Recovery = 20;
static constexpr uint32_t Sanity_Failures_Before_Fault = 2;
static constexpr uint32_t gnss_Startup_Qualification_Duration_Ms = 15000UL;
static constexpr uint32_t gnss_Startup_Qualification_PPS_Edges = 10;
static constexpr int64_t gnss_Startup_Min_PPS_Interval_Us = 800000LL;
static constexpr int64_t gnss_Startup_Max_PPS_Interval_Us = 1200000LL;

static constexpr char gnss_NVS_NAMESPACE[] = "gnss_state";
static constexpr char gnss_NVS_KEY_ID_TYPE[] = "id_type";
static constexpr char gnss_NVS_KEY_ID_VALUE[] = "id_value";
static constexpr char gnss_NVS_KEY_MAX_BAUD[] = "max_baud";
static constexpr char gnss_NVS_KEY_INITIAL_BAUD[] = "initial_baud";
static constexpr char gnss_NVS_KEY_ATTEMPT_NO_SIGNAL_RECOVERY[] = "no_sig_rcv";
static constexpr char restart_NVS_NAMESPACE[] = "restart_evt";
static constexpr char restart_NVS_KEY_PENDING[] = "pending";

static constexpr char gnss_ID_TYPE_UNIQID[] = "uniqid";
static constexpr char gnss_ID_TYPE_MODULE_FP[] = "module_fp";
static constexpr char gnss_ID_TYPE_GENERIC[] = "generic";
static constexpr char gnss_ID_VALUE_UNDETERMINED[] = "undetermined_gnss_board";

/* pre-release code - commented out
static constexpr bool reduceGNSSUART1OutputToTimeMessages = true;
static constexpr bool saveReducedGNSSUART1OutputPermanently = false;
*/
struct gnss_identity_t
{
    bool valid = false;
    char type[16] = "";
    char value[96] = "";
};

struct gnss_nvs_data_t
{
    bool has_stored_data = false;
    bool has_id_type = false;
    char id_type[16] = "";
    char id_value[96] = "";
    uint32_t initial_baud = 0;
    uint32_t max_baud = 0;
};

static uint32_t s_gnss_target_baud = 0;

struct nmea_rmc_time_t
{
    int year = 0;
    int month = 0;
    int day = 0;
    int hour = 0;
    int minute = 0;
    int second = 0;
};

static void refresh_sync_state_locked(sync_state_t *state, int64_t now_us)
{
    if (state == nullptr)
        return;

    bool sync_stale = state->last_successful_sync_us > 0 && (now_us - state->last_successful_sync_us) > Sync_Stale_After_Us;
    bool pps_missing = s_time_has_been_set.load() && !state->pps_active;
    bool gnss_missing = s_time_has_been_set.load() && (!state->gnss_timing_valid ||
                                                       state->last_gnss_valid_us == 0 ||
                                                       (now_us - state->last_gnss_valid_us) > Gnss_Validity_Timeout_Us);

    state->faults.sync_stale = sync_stale;
    state->faults.gnss_invalid = gnss_missing;
    state->faults.pps_missing = pps_missing;

#if DEBUG_ENABLED
    if (gnss_missing)
        ESP_LOGE(TAG, "GNSS invalid - GNSS missing.");
#endif

    state->holdover_mode = has_sync_fault(state->faults);
}

static void publish_ntp_sync_state_locked(const sync_state_t &state)
{
    s_ntp_sync_state_sequence.fetch_add(1, std::memory_order_release);
    s_ntp_last_successful_sync_us.store(state.last_successful_sync_us, std::memory_order_relaxed);
    s_ntp_last_gnss_valid_us.store(state.last_gnss_valid_us, std::memory_order_relaxed);
    s_ntp_pps_active.store(state.pps_active, std::memory_order_relaxed);
    s_ntp_gnss_timing_valid.store(state.gnss_timing_valid, std::memory_order_relaxed);
    s_ntp_pps_missing.store(state.faults.pps_missing, std::memory_order_relaxed);
    s_ntp_gnss_invalid.store(state.faults.gnss_invalid, std::memory_order_relaxed);
    s_ntp_sanity_mismatch.store(state.faults.sanity_mismatch, std::memory_order_relaxed);
    s_ntp_sync_stale.store(state.faults.sync_stale, std::memory_order_relaxed);
    s_ntp_sync_state_sequence.fetch_add(1, std::memory_order_release);
}

static void sync_state_note_attempt()
{
    if (xSemaphoreTake(s_sync_state_mutex, portMAX_DELAY) == pdTRUE)
    {
        s_sync_state.last_sync_attempt_us = esp_timer_get_time();
        refresh_sync_state_locked(&s_sync_state, s_sync_state.last_sync_attempt_us);
        publish_ntp_sync_state_locked(s_sync_state);
        xSemaphoreGive(s_sync_state_mutex);
    }
}

static void sync_state_note_pps_edge(int64_t edge_us)
{
    if (xSemaphoreTake(s_sync_state_mutex, portMAX_DELAY) == pdTRUE)
    {
        s_sync_state.last_pps_seen_us = edge_us;
        s_sync_state.pps_active = true;
        refresh_sync_state_locked(&s_sync_state, edge_us);
        publish_ntp_sync_state_locked(s_sync_state);
        xSemaphoreGive(s_sync_state_mutex);
    }
}

static void sync_state_note_pps_timeout(int64_t now_us)
{
#if MQTT_ENABLED && MQTT_HISTORICAL_REPORTING_ENABLED
    if (s_time_has_been_set.load() && !s_historical_pps_fault_active.exchange(true))
        s_last_pps_undisciplined.store(time(nullptr));
#endif

    if (xSemaphoreTake(s_sync_state_mutex, portMAX_DELAY) == pdTRUE)
    {
        s_sync_state.pps_active = false;
        refresh_sync_state_locked(&s_sync_state, now_us);
        publish_ntp_sync_state_locked(s_sync_state);
        xSemaphoreGive(s_sync_state_mutex);
    }
}

static void set_gnss_lock_state(bool valid)
{
    int64_t now_us = esp_timer_get_time();
    bool previous = s_gnss_locked.exchange(valid);
    if (previous == valid)
        return;

    if (valid)
    {
        s_gnss_lock_started_us.store(now_us);
    }
    else
    {
        int64_t lock_started_us = s_gnss_lock_started_us.exchange(0);
        if (lock_started_us > 0 && now_us > lock_started_us)
            s_gnss_locked_total_us.fetch_add(now_us - lock_started_us);
    }
}

static void sync_state_note_gnss_validity(bool valid)
{
    set_gnss_lock_state(valid);

#if MQTT_ENABLED && MQTT_HISTORICAL_REPORTING_ENABLED
    if (!valid && s_time_has_been_set.load() && !s_historical_gnss_fault_active.exchange(true))
        s_last_gnss_unsynchronized.store(time(nullptr));
#endif

    if (xSemaphoreTake(s_sync_state_mutex, portMAX_DELAY) == pdTRUE)
    {
        int64_t now_us = esp_timer_get_time();
        s_sync_state.gnss_timing_valid = valid;
        if (valid)
            s_sync_state.last_gnss_valid_us = now_us;
        refresh_sync_state_locked(&s_sync_state, now_us);
        publish_ntp_sync_state_locked(s_sync_state);
        xSemaphoreGive(s_sync_state_mutex);
    }
}

static uint32_t sync_state_note_failure(const sync_faults_t &faults, time_t update_delta)
{
    uint32_t failure_count = 0;

    if (faults.gnss_invalid)
        set_gnss_lock_state(false);

#if MQTT_ENABLED && MQTT_HISTORICAL_REPORTING_ENABLED
    if (s_time_has_been_set.load())
    {
        if (faults.gnss_invalid && !s_historical_gnss_fault_active.exchange(true))
            s_last_gnss_unsynchronized.store(time(nullptr));
        if (faults.pps_missing && !s_historical_pps_fault_active.exchange(true))
            s_last_pps_undisciplined.store(time(nullptr));
    }
#endif

    if (xSemaphoreTake(s_sync_state_mutex, portMAX_DELAY) == pdTRUE)
    {
        s_sync_state.last_sync_delta_seconds = update_delta;
        s_sync_state.consecutive_sync_failures++;
        s_sync_state.faults.pps_missing = s_sync_state.faults.pps_missing || faults.pps_missing;
        s_sync_state.faults.gnss_invalid = s_sync_state.faults.gnss_invalid || faults.gnss_invalid;
        s_sync_state.faults.sanity_mismatch = s_sync_state.faults.sanity_mismatch || faults.sanity_mismatch;
        s_sync_state.faults.sync_stale = s_sync_state.faults.sync_stale || faults.sync_stale;
        refresh_sync_state_locked(&s_sync_state, esp_timer_get_time());
        publish_ntp_sync_state_locked(s_sync_state);
        failure_count = s_sync_state.consecutive_sync_failures;
        xSemaphoreGive(s_sync_state_mutex);
    }

    return failure_count;
}

static uint32_t sync_state_note_sanity_retry(time_t update_delta)
{
    uint32_t failure_count = 0;

    if (xSemaphoreTake(s_sync_state_mutex, portMAX_DELAY) == pdTRUE)
    {
        s_sync_state.last_sync_delta_seconds = update_delta;
        s_sync_state.consecutive_sync_failures++;
        s_sync_state.consecutive_sanity_failures++;
        refresh_sync_state_locked(&s_sync_state, esp_timer_get_time());
        publish_ntp_sync_state_locked(s_sync_state);
        failure_count = s_sync_state.consecutive_sanity_failures;
        xSemaphoreGive(s_sync_state_mutex);
    }

    return failure_count;
}

static void sync_state_clear_sanity_failures()
{
    if (xSemaphoreTake(s_sync_state_mutex, portMAX_DELAY) == pdTRUE)
    {
        s_sync_state.consecutive_sanity_failures = 0;
        refresh_sync_state_locked(&s_sync_state, esp_timer_get_time());
        publish_ntp_sync_state_locked(s_sync_state);
        xSemaphoreGive(s_sync_state_mutex);
    }
}

static void sync_state_reset_failure_counters()
{
    if (xSemaphoreTake(s_sync_state_mutex, portMAX_DELAY) == pdTRUE)
    {
        s_sync_state.consecutive_sync_failures = 0;
        s_sync_state.consecutive_sanity_failures = 0;
        refresh_sync_state_locked(&s_sync_state, esp_timer_get_time());
        publish_ntp_sync_state_locked(s_sync_state);
        xSemaphoreGive(s_sync_state_mutex);
    }
}

static void sync_state_note_success(time_t update_delta)
{
    set_gnss_lock_state(true);

#if MQTT_ENABLED && MQTT_HISTORICAL_REPORTING_ENABLED
    bool recovery_completed = s_historical_gnss_fault_active.exchange(false) ||
                              s_historical_pps_fault_active.exchange(false);
    if (s_last_synchronized_and_disciplined.load() == 0 || recovery_completed)
        s_last_synchronized_and_disciplined.store(time(nullptr));
#endif

    if (xSemaphoreTake(s_sync_state_mutex, portMAX_DELAY) == pdTRUE)
    {
        s_sync_state.last_successful_sync_us = esp_timer_get_time();
        s_sync_state.gnss_timing_valid = true;
        s_sync_state.last_gnss_valid_us = s_sync_state.last_successful_sync_us;
        s_sync_state.last_sync_delta_seconds = update_delta;
        s_sync_state.consecutive_sync_failures = 0;
        s_sync_state.consecutive_sanity_failures = 0;
        s_sync_state.faults = {};
        refresh_sync_state_locked(&s_sync_state, s_sync_state.last_successful_sync_us);
        publish_ntp_sync_state_locked(s_sync_state);
        xSemaphoreGive(s_sync_state_mutex);
    }
}

static sync_state_t get_sync_state_snapshot()
{
    sync_state_t snapshot{};

    if (xSemaphoreTake(s_sync_state_mutex, portMAX_DELAY) == pdTRUE)
    {
        refresh_sync_state_locked(&s_sync_state, esp_timer_get_time());
        publish_ntp_sync_state_locked(s_sync_state);
        snapshot = s_sync_state;
        xSemaphoreGive(s_sync_state_mutex);
    }

    return snapshot;
}

static bool first_sync_candidates_are_plausible(const sync_candidate_t &first_candidate, const sync_candidate_t &second_candidate)
{
    time_t delta = second_candidate.candidate_time - first_candidate.candidate_time;
    return delta >= 1 && delta <= 3;
}

#if LIQUID_CRYSTAL_DISPLAY_ENABLED
static esp_err_t lcd_write_i2c(const hd44780_t *lcd, uint8_t data)
{
    (void)lcd;
    return pcf8574_port_write(&s_lcd_io, data);
}

static void init_lcd_descriptor()
{
    memset(&s_lcd, 0, sizeof(s_lcd));
    s_lcd.write_cb = lcd_write_i2c;
    s_lcd.font = HD44780_FONT_5X8;
    s_lcd.lines = lcdRows;
    s_lcd.pins.rs = 0;
    s_lcd.pins.e = 2;
    s_lcd.pins.d4 = 4;
    s_lcd.pins.d5 = 5;
    s_lcd.pins.d6 = 6;
    s_lcd.pins.d7 = 7;
    s_lcd.pins.bl = 3;
    s_lcd.backlight = true;
}

static void display_line(uint8_t row, const char *text)
{

    // LCD rows once displayed are cached and only updated when changed

    char padded[lcdColumns + 1];
    memset(padded, ' ', sizeof(padded) - 1);
    padded[lcdColumns] = '\0';

    if (text != nullptr)
    {
        size_t len = strlen(text);
        if (len > lcdColumns)
        {
            len = lcdColumns;
        }
        memcpy(padded, text, len);
    }

    if (!s_lcd_ready)
    {
#if DEBUG_ENABLED
        ESP_LOGW(TAG, "LCD not ready for row %u", row);
#endif
        return;
    }

    if (s_lcd_mutex != nullptr)
        xSemaphoreTake(s_lcd_mutex, portMAX_DELAY);

    if (row < lcdRows && s_lcd_line_cached[row] && strcmp(s_lcd_last_lines[row], padded) == 0)
    {
        if (s_lcd_mutex != nullptr)
            xSemaphoreGive(s_lcd_mutex);
        return;
    }

    esp_err_t err = hd44780_gotoxy(&s_lcd, 0, row);
    if (err != ESP_OK)
    {
#if DEBUG_ENABLED
        ESP_LOGE(TAG, "hd44780_gotoxy failed: %s", esp_err_to_name(err));
#endif
        if (s_lcd_mutex != nullptr)
            xSemaphoreGive(s_lcd_mutex);
        return;
    }

    err = hd44780_puts(&s_lcd, padded);
    if (err != ESP_OK)
    {
#if DEBUG_ENABLED
        ESP_LOGE(TAG, "hd44780_puts failed: %s", esp_err_to_name(err));
#endif
    }
    else if (row < lcdRows)
    {
        memcpy(s_lcd_last_lines[row], padded, sizeof(s_lcd_last_lines[row]));
        s_lcd_line_cached[row] = true;
    }

    if (s_lcd_mutex != nullptr)
        xSemaphoreGive(s_lcd_mutex);
}

static esp_err_t lcd_try_device_address(uint8_t address)
{
    uint8_t port_state = 0;

    memset(&s_lcd_io, 0, sizeof(s_lcd_io));
    esp_err_t err = pcf8574_init_desc(&s_lcd_io, address, LCD_I2C_PORT, LCD_I2C_SDA_GPIO, LCD_I2C_SCL_GPIO);
    if (err != ESP_OK)
        return err;

    err = pcf8574_port_read(&s_lcd_io, &port_state);
    if (err != ESP_OK)
    {
        pcf8574_free_desc(&s_lcd_io);
        memset(&s_lcd_io, 0, sizeof(s_lcd_io));
        return err;
    }

    s_lcd_addr = address;
    return ESP_OK;
}

static esp_err_t setup_lcd()
{
    init_lcd_descriptor();

    esp_err_t err = i2cdev_init();
    if (err != ESP_OK)
        return err;

    err = lcd_try_device_address(lcdI2CAddressPrimary);
    if (err != ESP_OK)
        err = lcd_try_device_address(lcdI2CAddressSecondary);

    if (err != ESP_OK)
        return err;

    err = hd44780_init(&s_lcd);
    if (err != ESP_OK)
        return err;

    err = hd44780_switch_backlight(&s_lcd, true);
    if (err != ESP_OK)
        return err;

    err = hd44780_control(&s_lcd, true, false, false);
    if (err != ESP_OK)
        return err;

    err = hd44780_clear(&s_lcd);
    if (err != ESP_OK)
        return err;

    s_lcd_ready = true;
    return ESP_OK;
}
#endif

static void display_selected_ip_address(int seconds)
{
    if (PreferIPvX == 9)
    {
        display_line(3, "");
        return;
    }

    static char last_known_IPv6_addresss[IP_ADDRESS_TEXT_SIZE] = "";

    static char ipv6_part1[IP_ADDRESS_TEXT_SIZE] = "";
    static char ipv6_part2[IP_ADDRESS_TEXT_SIZE] = "";

    network_address_snapshot_t addresses = get_network_address_snapshot();

    if (PreferIPvX == 8)
    {
        const char *ipv6_status = "N/A";
        if (addresses.ipv6[0] != '\0')
        {
            switch (addresses.ipv6_priority)
            {
            case ipv6_address_priority_t::global_unicast:
                ipv6_status = "GUA";
                break;
            case ipv6_address_priority_t::unique_local:
                ipv6_status = "ULA";
                break;
            case ipv6_address_priority_t::link_local:
                ipv6_status = "LLA";
                break;
            default:
                break;
            }
        }
        char status_line[lcdColumns + 1];
        snprintf(status_line, sizeof(status_line), "IPv4: %s  IPv6: %s", addresses.ipv4[0] != '\0' ? "OK" : "N/A", ipv6_status);
        display_line(3, status_line);
        return;
    }

    // if no IP address is selected, clear the display line
    if (addresses.selected[0] == '\0')
    {
        display_line(3, "");
        return;
    }

    // An IPv6 can change from Link-Local Address (LLA) to Unique-Local Address (ULA) to Global-Unicast Address (GUA)
    // so if the selected IPv6 address has changed reset the IPv6 address parts
    if (PreferIPvX == 0 || PreferIPvX == 2 || PreferIPvX == 6)
    {
        if (strcmp(addresses.ipv6, last_known_IPv6_addresss) != 0)
        {
            size_t total_len = strlen(addresses.ipv6);
            if (total_len == 0)
            {
                ipv6_part1[0] = '\0';
                ipv6_part2[0] = '\0';
                last_known_IPv6_addresss[0] = '\0';
            }
            else
            {
                size_t half_len = total_len / 2;
                while (half_len > 0 && addresses.ipv6[half_len] != ':')
                    half_len--;

                size_t remainder_len = total_len - half_len;
                strncpy(ipv6_part1, addresses.ipv6, half_len);
                ipv6_part1[half_len] = '\0';
                strncpy(ipv6_part2, addresses.ipv6 + half_len, remainder_len);
                ipv6_part2[remainder_len] = '\0';

                strncpy(last_known_IPv6_addresss, addresses.ipv6, IP_ADDRESS_TEXT_SIZE - 1);
                last_known_IPv6_addresss[IP_ADDRESS_TEXT_SIZE - 1] = '\0';
            }
        }
    }

    switch (PreferIPvX)
    {
    case 0:

        // no preference between IPv4 and IPv6
        // each minute:
        // display the IPv4 address for the first 20 seconds
        // display the first part of the IPv6 address in next 20 seconds
        // display the second part of the IPv6 address in the last 20 seconds

        if (seconds < 20)
            display_line(3, addresses.ipv4);
        else if (seconds < 40)
            display_line(3, ipv6_part1);
        else
            display_line(3, ipv6_part2);

        break;

    case 1:
    case 4:
        // Show the IPv4 address only
        if (strcmp(addresses.selected, addresses.ipv4) == 0)
        {
            display_line(3, addresses.selected);
            return;
        }
        break;

    case 2:
    case 6:
        // Show the IPv6 address only

        // each minute:
        // display the first part of the IPv6 address for the first 30 seconds
        // display the second part of the IPv6 address for the next 30 seconds
        if (seconds < 30)
            display_line(3, ipv6_part1);
        else
            display_line(3, ipv6_part2);
        break;
    }
}

static void apply_timezone_settings()
{
    setenv("TZ", timeZoneSpec, 1);
    tzset();
}

static void format_local_date_time(time_t utc_time, char *date_string, size_t date_size, char *time_string, size_t time_size)
{
    struct tm local_tm{};
    localtime_r(&utc_time, &local_tm);

    snprintf(date_string, date_size, "%04d-%02d-%02d", local_tm.tm_year + 1900, local_tm.tm_mon + 1, local_tm.tm_mday);

    int hour_value = local_tm.tm_hour;
    if (!display24HourFormat)
    {
        hour_value %= 12;
        if (hour_value == 0)
            hour_value = 12;
    }

    char zone[8] = "";

    if (displayTimeZone)
        strftime(zone, sizeof(zone), "%Z", &local_tm);

    const char *hour_format = displayHoursWithPaddedZero ? "%02d:%02d:%02d" : "%d:%02d:%02d";
    int len = snprintf(time_string, time_size, hour_format, hour_value, local_tm.tm_min, local_tm.tm_sec);

    if (!display24HourFormat && len >= 0 && static_cast<size_t>(len) < time_size)
        len += snprintf(time_string + len, time_size - len, " %s", local_tm.tm_hour < 12 ? "AM" : "PM");

    if (displayTimeZone && zone[0] != '\0' && len >= 0 && static_cast<size_t>(len) < time_size)
        snprintf(time_string + len, time_size - len, " %s", zone);
}

#if UPTIME_RESTART_BUTTON_ENABLED
static void get_uptime(char *buffer, size_t buffer_size)
{
    uint64_t total_seconds = static_cast<uint64_t>(esp_timer_get_time() / 1000000ULL);
    uint64_t days = total_seconds / 86400ULL;
    total_seconds %= 86400ULL;
    uint64_t hours = total_seconds / 3600ULL;
    total_seconds %= 3600ULL;
    uint64_t minutes = total_seconds / 60ULL;
    uint64_t seconds = total_seconds % 60ULL;
    snprintf(buffer, buffer_size, "%llu %02llu:%02llu:%02llu", days, hours, minutes, seconds);
}
#endif

static bool initialize_nvs_storage()
{
    esp_err_t err = nvs_flash_init();
    if (err == ESP_ERR_NVS_NO_FREE_PAGES || err == ESP_ERR_NVS_NEW_VERSION_FOUND)
    {
        ESP_LOGE(TAG, "NVS recovery requires operator action; automatic erase is disabled to preserve authentication storage");
        return false;
    }

    if (err != ESP_OK)
    {
#if DEBUG_ENABLED
        ESP_LOGE(TAG, "nvs_flash_init failed: %s", esp_err_to_name(err));
#endif
        return false;
    }

    return true;
}

static bool parse_mac_id_string(const char *text, uint8_t mac[6])
{
    if (text == nullptr || mac == nullptr || text[0] == '\0' || std::strlen(text) != 17)
        return false;

    if (text[2] != ':' || text[5] != ':' || text[8] != ':' || text[11] != ':' || text[14] != ':')
        return false;

    unsigned int values[6] = {};
    if (std::sscanf(text,
                    "%2x:%2x:%2x:%2x:%2x:%2x",
                    &values[0],
                    &values[1],
                    &values[2],
                    &values[3],
                    &values[4],
                    &values[5]) != 6)
        return false;

    for (size_t index = 0; index < 6; ++index)
        mac[index] = static_cast<uint8_t>(values[index]);

    return true;
}

static uint32_t get_highest_candidate_gnss_baud()
{
    return 921600;
}

static void build_candidate_baud_rates(std::vector<uint32_t> &out)
{
    static constexpr uint32_t all_candidate_baud_rates[] = {4800, 9600, 19200, 38400, 57600, 115200, 230400, 460800, 921600};

    out.assign(std::begin(all_candidate_baud_rates), std::end(all_candidate_baud_rates));
}

static bool load_gnss_nvs_data(gnss_nvs_data_t *data)
{
    if (data == nullptr)
        return false;

    *data = gnss_nvs_data_t{};

    nvs_handle_t handle = 0;
    esp_err_t err = nvs_open(gnss_NVS_NAMESPACE, NVS_READONLY, &handle);
    if (err == ESP_ERR_NVS_NOT_FOUND)
        return true;
    if (err != ESP_OK)
        return false;

    bool has_id_type_key = false;
    size_t type_length = 0;
    err = nvs_get_str(handle, gnss_NVS_KEY_ID_TYPE, nullptr, &type_length);
    if (err == ESP_OK && type_length > 0)
    {
        has_id_type_key = true;
        if (type_length > sizeof(data->id_type))
            type_length = sizeof(data->id_type);
        if (nvs_get_str(handle, gnss_NVS_KEY_ID_TYPE, data->id_type, &type_length) == ESP_OK)
            data->has_id_type = data->id_type[0] != '\0';
    }

    bool has_id_value_key = false;
    size_t value_length = 0;
    err = nvs_get_str(handle, gnss_NVS_KEY_ID_VALUE, nullptr, &value_length);
    if (err == ESP_OK && value_length > 0)
    {
        has_id_value_key = true;
        if (value_length > sizeof(data->id_value))
            value_length = sizeof(data->id_value);
        (void)nvs_get_str(handle, gnss_NVS_KEY_ID_VALUE, data->id_value, &value_length);
    }

    bool has_initial_baud_key = nvs_get_u32(handle, gnss_NVS_KEY_INITIAL_BAUD, &data->initial_baud) == ESP_OK;
    bool has_max_baud_key = nvs_get_u32(handle, gnss_NVS_KEY_MAX_BAUD, &data->max_baud) == ESP_OK;

    data->has_stored_data = has_id_type_key || has_id_value_key || has_initial_baud_key || has_max_baud_key;

    nvs_close(handle);
    return true;
}

static bool save_gnss_nvs_data(const gnss_identity_t &identity, uint32_t initial_baud, uint32_t max_baud)
{
    if (!identity.valid || identity.type[0] == '\0' || identity.value[0] == '\0' || initial_baud == 0 || max_baud == 0)
        return false;

    nvs_handle_t handle = 0;
    esp_err_t err = nvs_open(gnss_NVS_NAMESPACE, NVS_READWRITE, &handle);
    if (err != ESP_OK)
        return false;

    uint32_t stored_initial_baud = 0;
    if (nvs_get_u32(handle, gnss_NVS_KEY_INITIAL_BAUD, &stored_initial_baud) == ESP_OK &&
        stored_initial_baud > 0 && stored_initial_baud < initial_baud)
        initial_baud = stored_initial_baud;

    err = nvs_set_str(handle, gnss_NVS_KEY_ID_TYPE, identity.type);
    if (err == ESP_OK)
        err = nvs_set_str(handle, gnss_NVS_KEY_ID_VALUE, identity.value);
    if (err == ESP_OK)
        err = nvs_set_u32(handle, gnss_NVS_KEY_INITIAL_BAUD, initial_baud);
    if (err == ESP_OK)
        err = nvs_set_u32(handle, gnss_NVS_KEY_MAX_BAUD, max_baud);
    if (err == ESP_OK)
        err = nvs_commit(handle);

    nvs_close(handle);
    return err == ESP_OK;
}

static bool save_gnss_nvs_initial_baud(uint32_t initial_baud)
{
    if (initial_baud == 0)
        return false;

    nvs_handle_t handle = 0;
    esp_err_t err = nvs_open(gnss_NVS_NAMESPACE, NVS_READWRITE, &handle);
    if (err == ESP_OK)
    {
        uint32_t stored_initial_baud = 0;
        if (nvs_get_u32(handle, gnss_NVS_KEY_INITIAL_BAUD, &stored_initial_baud) == ESP_OK &&
            stored_initial_baud > 0 && stored_initial_baud < initial_baud)
            initial_baud = stored_initial_baud;
        err = nvs_set_u32(handle, gnss_NVS_KEY_INITIAL_BAUD, initial_baud);
    }
    if (err == ESP_OK)
        err = nvs_commit(handle);

    if (handle != 0)
        nvs_close(handle);
    return err == ESP_OK;
}

static void clear_gnss_nvs_data()
{
    nvs_handle_t handle = 0;
    esp_err_t err = nvs_open(gnss_NVS_NAMESPACE, NVS_READWRITE, &handle);
    if (err != ESP_OK)
        return;

    err = nvs_erase_key(handle, gnss_NVS_KEY_ID_TYPE);
    if (err != ESP_OK && err != ESP_ERR_NVS_NOT_FOUND)
    {
        nvs_close(handle);
        return;
    }

    err = nvs_erase_key(handle, gnss_NVS_KEY_ID_VALUE);
    if (err != ESP_OK && err != ESP_ERR_NVS_NOT_FOUND)
    {
        nvs_close(handle);
        return;
    }

    err = nvs_erase_key(handle, gnss_NVS_KEY_INITIAL_BAUD);
    if (err != ESP_OK && err != ESP_ERR_NVS_NOT_FOUND)
    {
        nvs_close(handle);
        return;
    }

    err = nvs_erase_key(handle, gnss_NVS_KEY_MAX_BAUD);
    if (err != ESP_OK && err != ESP_ERR_NVS_NOT_FOUND)
    {
        nvs_close(handle);
        return;
    }

    err = nvs_erase_key(handle, gnss_NVS_KEY_ATTEMPT_NO_SIGNAL_RECOVERY);
    if (err != ESP_OK && err != ESP_ERR_NVS_NOT_FOUND)
    {
        nvs_close(handle);
        return;
    }

    (void)nvs_commit(handle);
    nvs_close(handle);
}

static gnss_identity_t query_gnss_identity()
{
    gnss_identity_t identity{};

    UBX_SEC_UNIQID_data_t unique_chip_data{};
    if (s_gnss.getUniqueChipId(&unique_chip_data, 2000))
    {
        const char *unique_chip_id = s_gnss.getUniqueChipIdStr(&unique_chip_data, 2000);
        if (unique_chip_id != nullptr && unique_chip_id[0] != '\0')
        {
            snprintf(identity.type, sizeof(identity.type), "%s", gnss_ID_TYPE_UNIQID);
            snprintf(identity.value, sizeof(identity.value), "%s", unique_chip_id);
            identity.valid = true;
            return identity;
        }
    }

    if (s_gnss.getModuleInfo(2000))
    {
        const char *module_name = s_gnss.getModuleName(2000);
        const char *firmware_type = s_gnss.getFirmwareType(2000);
        uint8_t firmware_high = s_gnss.getFirmwareVersionHigh(2000);
        uint8_t firmware_low = s_gnss.getFirmwareVersionLow(2000);
        uint8_t protocol_high = s_gnss.getProtocolVersionHigh(2000);
        uint8_t protocol_low = s_gnss.getProtocolVersionLow(2000);

        if (module_name != nullptr && module_name[0] != '\0')
        {
            snprintf(identity.type, sizeof(identity.type), "%s", gnss_ID_TYPE_MODULE_FP);
            snprintf(identity.value,
                     sizeof(identity.value),
                     "%s|%s|FW%u.%u|PR%u.%u",
                     module_name,
                     firmware_type == nullptr ? "" : firmware_type,
                     static_cast<unsigned int>(firmware_high),
                     static_cast<unsigned int>(firmware_low),
                     static_cast<unsigned int>(protocol_high),
                     static_cast<unsigned int>(protocol_low));
            identity.valid = true;
            return identity;
        }
    }

    snprintf(identity.type, sizeof(identity.type), "%s", gnss_ID_TYPE_GENERIC);
    snprintf(identity.value, sizeof(identity.value), "%s", gnss_ID_VALUE_UNDETERMINED);
    identity.valid = true;
    return identity;
}

static bool gnss_identity_matches(const gnss_nvs_data_t &stored, const gnss_identity_t &current)
{
    if (!stored.has_id_type || !current.valid)
        return false;

    return strcmp(stored.id_type, current.type) == 0 && strcmp(stored.id_value, current.value) == 0;
}

#if UPTIME_RESTART_BUTTON_ENABLED
static bool check_uptime_request()
{

    static bool button_was_pressed = false;
    static uint32_t button_press_start_ms = 0;

    bool button_pressed = gpio_get_level(static_cast<gpio_num_t>(upTimeRestartPin)) == 0;

    if (button_pressed)
    {
        vTaskDelay(pdMS_TO_TICKS(10));
        button_pressed = gpio_get_level(static_cast<gpio_num_t>(upTimeRestartPin)) == 0;
    }

    if (!button_pressed)
    {
        button_was_pressed = false;
        button_press_start_ms = 0;
        return false;
    }

    if (!button_was_pressed)
    {
        button_was_pressed = true;
        button_press_start_ms = millis();
    }
    else if (millis() - button_press_start_ms >= holdUpTimeRestartButtonForThisManySecondsToTriggerAReset * 1000UL)
    {
        clear_gnss_nvs_data();
        controlled_restart("manual_restart");
    }

    return true;
}
#endif

static int64_t days_from_civil(int year, unsigned month, unsigned day)
{
    year -= month <= 2;
    const int era = (year >= 0 ? year : year - 399) / 400;
    const unsigned yoe = static_cast<unsigned>(year - era * 400);
    const unsigned doy = (153U * (month + (month > 2 ? static_cast<unsigned>(-3) : 9U)) + 2U) / 5U + day - 1U;
    const unsigned doe = yoe * 365U + yoe / 4U - yoe / 100U + doy;
    return static_cast<int64_t>(era) * 146097LL + static_cast<int64_t>(doe) - 719468LL;
}

static time_t epoch_from_utc(int year, int month, int day, int hour, int minute, int second)
{
    int64_t days = days_from_civil(year, static_cast<unsigned>(month), static_cast<unsigned>(day));
    int64_t seconds = days * 86400LL + hour * 3600LL + minute * 60LL + second;
    return static_cast<time_t>(seconds);
}

static uint64_t get_current_time_in_ntp64_format()

{

    struct timeval now{};

    gettimeofday(&now, nullptr);

    uint64_t seconds = NTP_EPOCH_OFFSET + static_cast<uint64_t>(now.tv_sec);

    uint64_t fraction = (static_cast<uint64_t>(now.tv_usec) << 32) / 1000000ULL;

    return (seconds << 32) | fraction;
}

static void write_ntp_timestamp(uint8_t *reply, size_t offset, uint64_t timestamp)
{
    reply[offset + 0] = static_cast<uint8_t>((timestamp >> 56) & 0xFF);
    reply[offset + 1] = static_cast<uint8_t>((timestamp >> 48) & 0xFF);
    reply[offset + 2] = static_cast<uint8_t>((timestamp >> 40) & 0xFF);
    reply[offset + 3] = static_cast<uint8_t>((timestamp >> 32) & 0xFF);
    reply[offset + 4] = static_cast<uint8_t>((timestamp >> 24) & 0xFF);
    reply[offset + 5] = static_cast<uint8_t>((timestamp >> 16) & 0xFF);
    reply[offset + 6] = static_cast<uint8_t>((timestamp >> 8) & 0xFF);
    reply[offset + 7] = static_cast<uint8_t>(timestamp & 0xFF);
}

struct ntp_reply_status_t
{
    uint8_t leap_indicator = 3;
    uint8_t stratum = 16;
    const char *reference_id = "INIT";
    bool reference_time_valid = false;
    bool gnss_synchronized = false;
    bool pps_disciplined = false;
};

static ntp_reply_status_t get_ntp_reply_status()
{
    for (size_t attempt = 0; attempt < 3; ++attempt)
    {
        uint32_t sequence_before = s_ntp_sync_state_sequence.load(std::memory_order_acquire);
        if ((sequence_before & 1U) != 0)
            continue;

        int64_t last_successful_sync_us = s_ntp_last_successful_sync_us.load(std::memory_order_relaxed);
        int64_t last_gnss_valid_us = s_ntp_last_gnss_valid_us.load(std::memory_order_relaxed);
        bool pps_active = s_ntp_pps_active.load(std::memory_order_relaxed);
        bool gnss_timing_valid = s_ntp_gnss_timing_valid.load(std::memory_order_relaxed);
        sync_faults_t faults{
            s_ntp_pps_missing.load(std::memory_order_relaxed),
            s_ntp_gnss_invalid.load(std::memory_order_relaxed),
            s_ntp_sanity_mismatch.load(std::memory_order_relaxed),
            s_ntp_sync_stale.load(std::memory_order_relaxed)};

        if (sequence_before != s_ntp_sync_state_sequence.load(std::memory_order_acquire))
            continue;

        int64_t now_us = esp_timer_get_time();
        bool gnss_recent = gnss_timing_valid && last_gnss_valid_us > 0 &&
                           (now_us - last_gnss_valid_us) <= Gnss_Validity_Timeout_Us;
        bool sync_stale = last_successful_sync_us > 0 &&
                          (now_us - last_successful_sync_us) > Sync_Stale_After_Us;
        bool gnss_synchronized = gnss_recent && !sync_stale && !faults.gnss_invalid;
        bool stratum_one = s_time_has_been_set.load(std::memory_order_acquire) &&
                           !s_time_setting_in_progress.load(std::memory_order_acquire) &&
                           !has_sync_fault(faults) && pps_active && gnss_synchronized &&
                           s_ntp_reference_valid.load(std::memory_order_acquire);

        if (stratum_one)
            return {0, 1, "GPS", true, gnss_synchronized, pps_active};
        return {3, 16, "INIT", false, gnss_synchronized, pps_active};
    }

    return {};
}

static constexpr uint8_t NTP_REPLY_TEMPLATE[NTP_PACKET_SIZE] = {
    0, 0, 4, static_cast<uint8_t>(NTP_PRECISION_EXPONENT),
    0, 0, 0, 0,
    0, 0, 0, static_cast<uint8_t>(NTP_ROOT_DISPERSION)};

static void build_ntp_reply(const uint8_t *request, uint8_t *reply, uint8_t version, uint64_t receive_time, const ntp_reply_status_t &status)
{
    memcpy(reply, NTP_REPLY_TEMPLATE, sizeof(NTP_REPLY_TEMPLATE));

    reply[0] = static_cast<uint8_t>((status.leap_indicator << 6) | (version << 3) | 4);
    reply[1] = status.stratum;
    memcpy(reply + 12, status.reference_id, 4);

    if (status.reference_time_valid)
        write_ntp_timestamp(reply, 16, s_ntp_reference_time_64.load(std::memory_order_acquire));

    memcpy(reply + 24, request + 40, 8);
    write_ntp_timestamp(reply, 32, receive_time);
}

static constexpr size_t ETH_HEADER_SIZE = 14;
static constexpr size_t IPV4_HEADER_SIZE = 20;
static constexpr size_t IPV6_HEADER_SIZE = 40;
static constexpr size_t UDP_HEADER_SIZE = 8;
static constexpr size_t RAW_NTP_FRAME_SIZE = ETH_HEADER_SIZE + IPV4_HEADER_SIZE + UDP_HEADER_SIZE + NTP_MAX_PACKET_SIZE;
static constexpr size_t RAW_IPV6_NTP_FRAME_SIZE = ETH_HEADER_SIZE + IPV6_HEADER_SIZE + UDP_HEADER_SIZE + NTP_MAX_PACKET_SIZE;
static constexpr size_t HARDWARE_NTP_REQUEST_QUEUE_DEPTH = 256;
static constexpr size_t HARDWARE_NTP_REQUEST_BUFFER_COUNT = 64; // Do not increase this value, larger pools caused unacceptable internal/DMA-memory pressure
static constexpr size_t HARDWARE_NTP_REQUEST_BUFFER_SIZE = ETH_HEADER_SIZE + IPV6_HEADER_SIZE + 60 + UDP_HEADER_SIZE + NTP_MAX_PACKET_SIZE;
static constexpr uint32_t HARDWARE_NTP_TRANSMIT_RETRY_COUNT = 3;
static constexpr uint32_t HARDWARE_NTP_TRANSMIT_RETRY_DELAY_US = 10;
static constexpr uint32_t ETHERNET_RECOVERY_DELAY_MS = 100;
static constexpr uint32_t ETHERNET_RECOVERY_STOP_TIMEOUT_MS = 1000;
static constexpr uint32_t ETHERNET_RECOVERY_IP_TIMEOUT_MS = 10000;
static constexpr uint32_t ETHERNET_RECOVERY_RX_UNAVAILABLE_ATTEMPTS_BEFORE_RESTART = 2;
static constexpr int64_t NTP_TRANSPORT_STALL_TIMEOUT_US = 35000000LL;

struct hardware_ntp_request_t
{
    esp_eth_handle_t handle;
    uint8_t *frame;
    uint32_t length;
    esp_netif_t *netif;
    eth_mac_time_t rx_timestamp;
};

static QueueHandle_t s_hardware_ntp_request_queue = nullptr;
static QueueHandle_t s_hardware_ntp_request_buffer_queue = nullptr;
static TaskHandle_t s_ntp_cache_purge_task_handle = nullptr;
static TaskHandle_t s_hardware_ntp_server_task_handle = nullptr;
static uint8_t s_hardware_ntp_request_buffers[HARDWARE_NTP_REQUEST_BUFFER_COUNT][HARDWARE_NTP_REQUEST_BUFFER_SIZE]{};

static bool initialize_hardware_ntp_request_buffers()
{
    for (size_t index = 0; index < HARDWARE_NTP_REQUEST_BUFFER_COUNT; ++index)
    {
        uint8_t *buffer = s_hardware_ntp_request_buffers[index];
        if (xQueueSend(s_hardware_ntp_request_buffer_queue, &buffer, 0) != pdTRUE)
            return false;
    }
    return true;
}

static void release_hardware_ntp_request_buffer(uint8_t *buffer)
{
    if (buffer != nullptr && s_hardware_ntp_request_buffer_queue != nullptr)
        xQueueSend(s_hardware_ntp_request_buffer_queue, &buffer, 0);
}

static void deinitialize_hardware_ntp_server()
{
    s_hardware_ntp_accepting.store(false, std::memory_order_release);
    if (s_hardware_ntp_server_task_handle != nullptr)
    {
        vTaskDelete(s_hardware_ntp_server_task_handle);
        s_hardware_ntp_server_task_handle = nullptr;
    }
    if (s_ntp_cache_purge_task_handle != nullptr)
    {
        vTaskDelete(s_ntp_cache_purge_task_handle);
        s_ntp_cache_purge_task_handle = nullptr;
    }
    if (s_hardware_ntp_request_queue != nullptr)
    {
        vQueueDelete(s_hardware_ntp_request_queue);
        s_hardware_ntp_request_queue = nullptr;
    }
    if (s_hardware_ntp_request_buffer_queue != nullptr)
    {
        vQueueDelete(s_hardware_ntp_request_buffer_queue);
        s_hardware_ntp_request_buffer_queue = nullptr;
    }
    if (s_hardware_ntp_transmit_mutex != nullptr)
    {
        vSemaphoreDelete(s_hardware_ntp_transmit_mutex);
        s_hardware_ntp_transmit_mutex = nullptr;
    }
    ntp_cache_deinit();
}

static uint16_t internet_checksum(const uint8_t *data, size_t length)
{
    uint32_t sum = 0;
    while (length >= 2)
    {
        sum += static_cast<uint16_t>((data[0] << 8) | data[1]);
        data += 2;
        length -= 2;
    }
    if (length != 0)
        sum += static_cast<uint16_t>(data[0] << 8);
    while ((sum >> 16) != 0)
        sum = (sum & 0xFFFFU) + (sum >> 16);
    return static_cast<uint16_t>(~sum);
}

static uint64_t ntp64_from_hardware_timestamp(const eth_mac_time_t &timestamp)
{
    const uint64_t seconds = NTP_EPOCH_OFFSET + timestamp.seconds;
    const uint64_t fraction = (static_cast<uint64_t>(timestamp.nanoseconds) << 32) / 1000000000ULL;
    return (seconds << 32) | fraction;
}

static bool timestamp_is_valid(const eth_mac_time_t *timestamp)
{
    return timestamp != nullptr && (timestamp->seconds != 0 || timestamp->nanoseconds != 0);
}

static bool is_ipv4_ntp_request(const uint8_t *frame, uint32_t length, size_t *ip_offset, size_t *udp_offset)
{
    if (frame == nullptr || length < ETH_HEADER_SIZE + IPV4_HEADER_SIZE + UDP_HEADER_SIZE + NTP_PACKET_SIZE || frame[12] != 0x08 || frame[13] != 0x00)
        return false;

    const size_t ipv4_offset = ETH_HEADER_SIZE;
    const uint8_t version_ihl = frame[ipv4_offset];
    const size_t header_length = static_cast<size_t>(version_ihl & 0x0F) * 4;
    if ((version_ihl >> 4) != 4 || header_length < IPV4_HEADER_SIZE || length < ETH_HEADER_SIZE + header_length + UDP_HEADER_SIZE + NTP_PACKET_SIZE)
        return false;
    if (frame[ipv4_offset + 9] != IPPROTO_UDP)
        return false;

    const size_t udp_header_offset = ipv4_offset + header_length;
    const uint16_t udp_length = static_cast<uint16_t>((frame[udp_header_offset + 4] << 8) | frame[udp_header_offset + 5]);
    const uint16_t destination_port = static_cast<uint16_t>((frame[udp_header_offset + 2] << 8) | frame[udp_header_offset + 3]);
    if (destination_port != NTP_PORT || udp_length < UDP_HEADER_SIZE + NTP_PACKET_SIZE ||
        udp_length > UDP_HEADER_SIZE + NTP_MAX_PACKET_SIZE || udp_header_offset + udp_length > length)
        return false;

    *ip_offset = ipv4_offset;
    *udp_offset = udp_header_offset;
    return true;
}

static bool is_ipv6_extension_header(uint8_t next_header)
{
    return next_header == 0 || next_header == 43 || next_header == 60 || next_header == 135 || next_header == 51;
}

static bool is_ipv6_ntp_request(const uint8_t *frame, uint32_t length, size_t *ip_offset, size_t *udp_offset)
{
    if (frame == nullptr || length < ETH_HEADER_SIZE + IPV6_HEADER_SIZE + UDP_HEADER_SIZE + NTP_PACKET_SIZE || frame[12] != 0x86 || frame[13] != 0xDD)
        return false;

    const size_t ipv6_offset = ETH_HEADER_SIZE;
    if ((frame[ipv6_offset] >> 4) != 6)
        return false;

    const size_t payload_length = static_cast<size_t>((frame[ipv6_offset + 4] << 8) | frame[ipv6_offset + 5]);
    const size_t payload_end = ipv6_offset + IPV6_HEADER_SIZE + payload_length;
    if (payload_end > length)
        return false;

    uint8_t next_header = frame[ipv6_offset + 6];
    size_t offset = ipv6_offset + IPV6_HEADER_SIZE;
    for (size_t count = 0; is_ipv6_extension_header(next_header); ++count)
    {
        if (count == 8 || offset + 2 > payload_end)
            return false;
        const size_t extension_length = next_header == 51
                                            ? static_cast<size_t>(frame[offset + 1] + 2) * 4
                                            : static_cast<size_t>(frame[offset + 1] + 1) * 8;
        if (extension_length < 8 || offset + extension_length > payload_end)
            return false;
        next_header = frame[offset];
        offset += extension_length;
    }

    if (next_header != IPPROTO_UDP || offset + UDP_HEADER_SIZE + NTP_PACKET_SIZE > payload_end)
        return false;

    const uint16_t udp_length = static_cast<uint16_t>((frame[offset + 4] << 8) | frame[offset + 5]);
    const uint16_t destination_port = static_cast<uint16_t>((frame[offset + 2] << 8) | frame[offset + 3]);
    if (destination_port != NTP_PORT || udp_length < UDP_HEADER_SIZE + NTP_PACKET_SIZE ||
        udp_length > UDP_HEADER_SIZE + NTP_MAX_PACKET_SIZE ||
        offset + udp_length != payload_end)
        return false;

    *ip_offset = ipv6_offset;
    *udp_offset = offset;
    return true;
}

static bool is_internal_ntp_ipv4_address(const struct in_addr &address)
{
    if (address.s_addr == htonl(INADDR_LOOPBACK))
        return true;

    const network_address_snapshot_t addresses = get_network_address_snapshot();
    struct in_addr assigned_address{};
    return addresses.ipv4[0] != '\0' && inet_pton(AF_INET, addresses.ipv4, &assigned_address) == 1 &&
           address.s_addr == assigned_address.s_addr;
}

static bool is_internal_ntp_ipv6_address(const struct in6_addr &address)
{
    struct in6_addr loopback_address{};
    if (inet_pton(AF_INET6, "::1", &loopback_address) == 1 &&
        memcmp(&address, &loopback_address, sizeof(address)) == 0)
        return true;

    const network_address_snapshot_t addresses = get_network_address_snapshot();
    struct in6_addr assigned_address{};
    return addresses.ipv6[0] != '\0' && inet_pton(AF_INET6, addresses.ipv6, &assigned_address) == 1 &&
           memcmp(&address, &assigned_address, sizeof(address)) == 0;
}

static bool is_internal_ntp_client(const struct sockaddr_storage &address)
{
    if (address.ss_family == AF_INET)
        return is_internal_ntp_ipv4_address(reinterpret_cast<const struct sockaddr_in *>(&address)->sin_addr);
    if (address.ss_family == AF_INET6)
        return is_internal_ntp_ipv6_address(reinterpret_cast<const struct sockaddr_in6 *>(&address)->sin6_addr);
    return false;
}

static uint16_t ipv6_udp_checksum(const uint8_t *source, const uint8_t *destination, const uint8_t *udp, size_t udp_length)
{
    uint8_t checksum_data[IPV6_HEADER_SIZE + UDP_HEADER_SIZE + NTP_MAX_PACKET_SIZE] = {};
    memcpy(checksum_data, source, 16);
    memcpy(checksum_data + 16, destination, 16);
    checksum_data[35] = static_cast<uint8_t>(udp_length);
    checksum_data[39] = IPPROTO_UDP;
    memcpy(checksum_data + IPV6_HEADER_SIZE, udp, udp_length);
    const uint16_t checksum = internet_checksum(checksum_data, IPV6_HEADER_SIZE + udp_length);
    return checksum == 0 ? 0xFFFF : checksum;
}

static uint64_t read_ntp_timestamp(const uint8_t *packet, size_t offset);

static esp_err_t process_hardware_ntp_request(esp_eth_handle_t handle, uint8_t *frame, uint32_t length, void *netif, void *info)
{
    size_t ip_offset = 0;
    size_t udp_offset = 0;
    const eth_mac_time_t *rx_timestamp = static_cast<const eth_mac_time_t *>(info);
    if (!is_ipv4_ntp_request(frame, length, &ip_offset, &udp_offset) || !timestamp_is_valid(rx_timestamp))
    {
        release_hardware_ntp_request_buffer(frame);
        return ESP_OK;
    }

    const eth_mac_time_t receive_timestamp = *rx_timestamp;
    const uint8_t *request = frame + udp_offset + UDP_HEADER_SIZE;
    const uint8_t version = (request[0] >> 3) & 0x07;
    const uint8_t mode = request[0] & 0x07;
    if (version < 3 || version > 4 || mode != 3)
    {
        release_hardware_ntp_request_buffer(frame);
        return ESP_OK;
    }

#if SYMMETRIC_KEY_AUTHENTICATION_ENABLED
    const size_t request_length = static_cast<size_t>((frame[udp_offset + 4] << 8) | frame[udp_offset + 5]) - UDP_HEADER_SIZE;
    uint32_t authentication_key_id = 0;
    const ntp_auth_result_t authentication_result = ntp_auth_verify_request(request, request_length, version, &authentication_key_id);
    if (authentication_result != ntp_auth_result_t::unauthenticated && authentication_result != ntp_auth_result_t::valid)
    {
#if MQTT_ENABLED
        s_ntp_invalid_requests.fetch_add(1, std::memory_order_relaxed);
        if (version == 4)
            s_ntp_authenticated_invalid_requests.fetch_add(1, std::memory_order_relaxed);
        else
            s_ntp_unauthenticated_invalid_requests.fetch_add(1, std::memory_order_relaxed);
        s_ntp_requests_this_second.fetch_add(1, std::memory_order_relaxed);
#endif
        release_hardware_ntp_request_buffer(frame);
        return ESP_OK;
    }
    const bool authenticated_request = authentication_result == ntp_auth_result_t::valid;
#else
    const bool authenticated_request = false;
#endif

    const uint32_t client_ip = (static_cast<uint32_t>(frame[ip_offset + 12]) << 24) |
                               (static_cast<uint32_t>(frame[ip_offset + 13]) << 16) |
                               (static_cast<uint32_t>(frame[ip_offset + 14]) << 8) |
                               frame[ip_offset + 15];
    const uint16_t client_port = static_cast<uint16_t>((frame[udp_offset] << 8) | frame[udp_offset + 1]);
    ntp_client_record_t client_record{};
    if (!ntp_cache_find_or_create(client_ip, client_port, &client_record))
    {
        release_hardware_ntp_request_buffer(frame);
        return ESP_OK;
    }

    const uint64_t receive_time = ntp64_from_hardware_timestamp(receive_timestamp);
#if MQTT_ENABLED
    struct sockaddr_storage source_address{};
    auto *source_ipv4_address = reinterpret_cast<struct sockaddr_in *>(&source_address);
    source_ipv4_address->sin_family = AF_INET;
    source_ipv4_address->sin_port = htons(client_port);
    memcpy(&source_ipv4_address->sin_addr, frame + ip_offset + 12, sizeof(source_ipv4_address->sin_addr));
    s_ntp_valid_requests.fetch_add(1, std::memory_order_relaxed);
    if (authenticated_request)
        s_ntp_authenticated_valid_requests.fetch_add(1, std::memory_order_relaxed);
    else
        s_ntp_unauthenticated_valid_requests.fetch_add(1, std::memory_order_relaxed);
    mqtt_enqueue_ntp_request(source_address);
#endif
    uint8_t reply[NTP_MAX_PACKET_SIZE] = {};
    const ntp_reply_status_t status = get_ntp_reply_status();
#if MQTT_ENABLED
    if (status.gnss_synchronized && status.pps_disciplined)
        s_ntp_responses_synchronized_and_disciplined.fetch_add(1, std::memory_order_relaxed);
    if (!status.gnss_synchronized)
        s_ntp_responses_gnss_unsynchronized.fetch_add(1, std::memory_order_relaxed);
    if (!status.pps_disciplined)
        s_ntp_responses_pps_undisciplined.fetch_add(1, std::memory_order_relaxed);
#endif
    build_ntp_reply(request, reply, version, receive_time, status);

    const uint64_t client_receive_timestamp =
        (static_cast<uint64_t>(request[32]) << 56) | (static_cast<uint64_t>(request[33]) << 48) |
        (static_cast<uint64_t>(request[34]) << 40) | (static_cast<uint64_t>(request[35]) << 32) |
        (static_cast<uint64_t>(request[36]) << 24) | (static_cast<uint64_t>(request[37]) << 16) |
        (static_cast<uint64_t>(request[38]) << 8) | request[39];
    const uint64_t client_origin_timestamp =
        (static_cast<uint64_t>(request[24]) << 56) | (static_cast<uint64_t>(request[25]) << 48) |
        (static_cast<uint64_t>(request[26]) << 40) | (static_cast<uint64_t>(request[27]) << 32) |
        (static_cast<uint64_t>(request[28]) << 24) | (static_cast<uint64_t>(request[29]) << 16) |
        (static_cast<uint64_t>(request[30]) << 8) | request[31];
    const uint64_t client_transmit_timestamp =
        (static_cast<uint64_t>(request[40]) << 56) | (static_cast<uint64_t>(request[41]) << 48) |
        (static_cast<uint64_t>(request[42]) << 40) | (static_cast<uint64_t>(request[43]) << 32) |
        (static_cast<uint64_t>(request[44]) << 24) | (static_cast<uint64_t>(request[45]) << 16) |
        (static_cast<uint64_t>(request[46]) << 8) | request[47];
    const uint64_t previous_t2 = client_record.prev_t2;
    const uint64_t previous_t3 = client_record.prev_t3;
    const bool interleaved_reply = previous_t2 != 0 &&
                                   client_receive_timestamp != client_transmit_timestamp &&
                                   client_origin_timestamp == previous_t2;
    if (interleaved_reply)
    {
        write_ntp_timestamp(reply, 24, client_receive_timestamp);
        write_ntp_timestamp(reply, 40, previous_t3);
    }
    else
    {
        write_ntp_timestamp(reply, 40, get_current_time_in_ntp64_format());
    }

    uint8_t response_frame[RAW_NTP_FRAME_SIZE] = {};
    memcpy(response_frame, frame + 6, 6);
    memcpy(response_frame + 6, frame, 6);
    response_frame[12] = 0x08;
    response_frame[13] = 0x00;
    uint8_t *ip = response_frame + ETH_HEADER_SIZE;
    ip[0] = 0x45;
    ip[2] = 0;
    ip[3] = IPV4_HEADER_SIZE + UDP_HEADER_SIZE + NTP_PACKET_SIZE;
    ip[8] = 64;
    ip[9] = IPPROTO_UDP;
    memcpy(ip + 12, frame + ip_offset + 16, 4);
    memcpy(ip + 16, frame + ip_offset + 12, 4);
    const uint16_t checksum = internet_checksum(ip, IPV4_HEADER_SIZE);
    ip[10] = static_cast<uint8_t>(checksum >> 8);
    ip[11] = static_cast<uint8_t>(checksum);
    uint8_t *udp = ip + IPV4_HEADER_SIZE;
    udp[0] = 0;
    udp[1] = static_cast<uint8_t>(NTP_PORT);
    udp[2] = frame[udp_offset];
    udp[3] = frame[udp_offset + 1];
    udp[4] = 0;
    udp[5] = UDP_HEADER_SIZE + NTP_PACKET_SIZE;
    memcpy(udp + UDP_HEADER_SIZE, reply, NTP_PACKET_SIZE);

    esp_err_t result = ESP_ERR_INVALID_STATE;
    if (s_hardware_ntp_accepting.load(std::memory_order_acquire) &&
        s_hardware_ntp_transmit_mutex != nullptr)
    {
        if (xSemaphoreTake(s_hardware_ntp_transmit_mutex, portMAX_DELAY) == pdTRUE)
        {
            if (s_hardware_ntp_accepting.load(std::memory_order_acquire))
            {
                for (uint32_t attempt = 0; attempt < HARDWARE_NTP_TRANSMIT_RETRY_COUNT; ++attempt)
                {
                    if (!interleaved_reply)
                    {
                        write_ntp_timestamp(reply, 40, get_current_time_in_ntp64_format());
                    }

                    size_t reply_length = NTP_PACKET_SIZE;
#if SYMMETRIC_KEY_AUTHENTICATION_ENABLED
                    if (authenticated_request && !ntp_auth_append_response(reply, sizeof(reply), &reply_length, authentication_key_id))
                        break;
#endif
                    ip[2] = static_cast<uint8_t>((IPV4_HEADER_SIZE + UDP_HEADER_SIZE + reply_length) >> 8);
                    ip[3] = static_cast<uint8_t>(IPV4_HEADER_SIZE + UDP_HEADER_SIZE + reply_length);
                    ip[10] = 0;
                    ip[11] = 0;
                    const uint16_t refreshed_ip_checksum = internet_checksum(ip, IPV4_HEADER_SIZE);
                    ip[10] = static_cast<uint8_t>(refreshed_ip_checksum >> 8);
                    ip[11] = static_cast<uint8_t>(refreshed_ip_checksum);
                    udp[4] = static_cast<uint8_t>((UDP_HEADER_SIZE + reply_length) >> 8);
                    udp[5] = static_cast<uint8_t>(UDP_HEADER_SIZE + reply_length);
                    memcpy(udp + UDP_HEADER_SIZE, reply, reply_length);

                    result = esp_eth_transmit(handle, response_frame, ETH_HEADER_SIZE + IPV4_HEADER_SIZE + UDP_HEADER_SIZE + reply_length);
                    if (result != ESP_ERR_NO_MEM)
                        break;
                    esp_rom_delay_us(HARDWARE_NTP_TRANSMIT_RETRY_DELAY_US);
                }
            }
            xSemaphoreGive(s_hardware_ntp_transmit_mutex);
        }
    }
    if (result == ESP_OK)
    {
        ntp_cache_update(client_ip, client_port, receive_time, read_ntp_timestamp(reply, 40));
        const int64_t response_us = esp_timer_get_time();
        s_last_hardware_ntp_response_us.store(response_us, std::memory_order_release);
        s_last_ntp_response_us.store(response_us, std::memory_order_relaxed);
#if MQTT_ENABLED
        s_ntp_responses.fetch_add(1, std::memory_order_relaxed);
#endif
    }

    release_hardware_ntp_request_buffer(frame);
    return result;
}

static uint64_t read_ntp_timestamp(const uint8_t *packet, size_t offset)
{
    return (static_cast<uint64_t>(packet[offset]) << 56) |
           (static_cast<uint64_t>(packet[offset + 1]) << 48) |
           (static_cast<uint64_t>(packet[offset + 2]) << 40) |
           (static_cast<uint64_t>(packet[offset + 3]) << 32) |
           (static_cast<uint64_t>(packet[offset + 4]) << 24) |
           (static_cast<uint64_t>(packet[offset + 5]) << 16) |
           (static_cast<uint64_t>(packet[offset + 6]) << 8) |
           static_cast<uint64_t>(packet[offset + 7]);
}

static esp_err_t process_hardware_ipv6_ntp_request(esp_eth_handle_t handle, uint8_t *frame, uint32_t length, void *netif, void *info)
{
    size_t ip_offset = 0;
    size_t udp_offset = 0;
    const eth_mac_time_t *rx_timestamp = static_cast<const eth_mac_time_t *>(info);
    if (!is_ipv6_ntp_request(frame, length, &ip_offset, &udp_offset) || !timestamp_is_valid(rx_timestamp))
    {
        release_hardware_ntp_request_buffer(frame);
        return ESP_OK;
    }

    const eth_mac_time_t receive_timestamp = *rx_timestamp;
    const uint8_t *request = frame + udp_offset + UDP_HEADER_SIZE;
    const uint8_t version = (request[0] >> 3) & 0x07;
    const uint8_t mode = request[0] & 0x07;
    if (version < 3 || version > 4 || mode != 3)
    {
        release_hardware_ntp_request_buffer(frame);
        return ESP_OK;
    }

#if SYMMETRIC_KEY_AUTHENTICATION_ENABLED
    const size_t request_length = static_cast<size_t>((frame[udp_offset + 4] << 8) | frame[udp_offset + 5]) - UDP_HEADER_SIZE;
    uint32_t authentication_key_id = 0;
    const ntp_auth_result_t authentication_result = ntp_auth_verify_request(request, request_length, version, &authentication_key_id);
    if (authentication_result != ntp_auth_result_t::unauthenticated && authentication_result != ntp_auth_result_t::valid)
    {
#if MQTT_ENABLED
        s_ntp_invalid_requests.fetch_add(1, std::memory_order_relaxed);
        if (version == 4)
            s_ntp_authenticated_invalid_requests.fetch_add(1, std::memory_order_relaxed);
        else
            s_ntp_unauthenticated_invalid_requests.fetch_add(1, std::memory_order_relaxed);
        s_ntp_requests_this_second.fetch_add(1, std::memory_order_relaxed);
#endif
        release_hardware_ntp_request_buffer(frame);
        return ESP_OK;
    }
    const bool authenticated_request = authentication_result == ntp_auth_result_t::valid;
#else
    const bool authenticated_request = false;
#endif

    struct in6_addr client_ip{};
    memcpy(&client_ip, frame + ip_offset + 8, sizeof(client_ip));
    const uint16_t client_port = static_cast<uint16_t>((frame[udp_offset] << 8) | frame[udp_offset + 1]);
    ntp_client_record_ipv6_t client_record{};
    if (!ntp_cache_find_or_create_ipv6(&client_ip, client_port, &client_record))
    {
        release_hardware_ntp_request_buffer(frame);
        return ESP_OK;
    }

    const uint64_t receive_time = ntp64_from_hardware_timestamp(receive_timestamp);
#if MQTT_ENABLED
    struct sockaddr_storage source_address{};
    auto *source_ipv6_address = reinterpret_cast<struct sockaddr_in6 *>(&source_address);
    source_ipv6_address->sin6_family = AF_INET6;
    source_ipv6_address->sin6_port = htons(client_port);
    source_ipv6_address->sin6_scope_id = esp_netif_get_netif_impl_index(static_cast<esp_netif_t *>(netif));
    source_ipv6_address->sin6_addr = client_ip;
    s_ntp_valid_requests.fetch_add(1, std::memory_order_relaxed);
    if (authenticated_request)
        s_ntp_authenticated_valid_requests.fetch_add(1, std::memory_order_relaxed);
    else
        s_ntp_unauthenticated_valid_requests.fetch_add(1, std::memory_order_relaxed);
    mqtt_enqueue_ntp_request(source_address);
#endif
    uint8_t reply[NTP_MAX_PACKET_SIZE] = {};
    const ntp_reply_status_t status = get_ntp_reply_status();
#if MQTT_ENABLED
    if (status.gnss_synchronized && status.pps_disciplined)
        s_ntp_responses_synchronized_and_disciplined.fetch_add(1, std::memory_order_relaxed);
    if (!status.gnss_synchronized)
        s_ntp_responses_gnss_unsynchronized.fetch_add(1, std::memory_order_relaxed);
    if (!status.pps_disciplined)
        s_ntp_responses_pps_undisciplined.fetch_add(1, std::memory_order_relaxed);
#endif
    build_ntp_reply(request, reply, version, receive_time, status);

    const uint64_t client_receive_timestamp = read_ntp_timestamp(request, 32);
    const uint64_t client_origin_timestamp = read_ntp_timestamp(request, 24);
    const uint64_t client_transmit_timestamp = read_ntp_timestamp(request, 40);
    const bool interleaved_reply = client_record.prev_t2 != 0 &&
                                   client_receive_timestamp != client_transmit_timestamp &&
                                   client_origin_timestamp == client_record.prev_t2;
    if (interleaved_reply)
    {
        write_ntp_timestamp(reply, 24, client_receive_timestamp);
        write_ntp_timestamp(reply, 40, client_record.prev_t3);
    }
    else
    {
        write_ntp_timestamp(reply, 40, get_current_time_in_ntp64_format());
    }

    uint8_t response_frame[RAW_IPV6_NTP_FRAME_SIZE] = {};
    memcpy(response_frame, frame + 6, 6);
    memcpy(response_frame + 6, frame, 6);
    response_frame[12] = 0x86;
    response_frame[13] = 0xDD;
    uint8_t *ip = response_frame + ETH_HEADER_SIZE;
    ip[0] = 0x60;
    ip[5] = UDP_HEADER_SIZE + NTP_PACKET_SIZE;
    ip[6] = IPPROTO_UDP;
    ip[7] = 64;
    memcpy(ip + 8, frame + ip_offset + 24, 16);
    memcpy(ip + 24, frame + ip_offset + 8, 16);
    uint8_t *udp = ip + IPV6_HEADER_SIZE;
    udp[1] = static_cast<uint8_t>(NTP_PORT);
    udp[2] = frame[udp_offset];
    udp[3] = frame[udp_offset + 1];
    udp[5] = UDP_HEADER_SIZE + NTP_PACKET_SIZE;
    memcpy(udp + UDP_HEADER_SIZE, reply, NTP_PACKET_SIZE);
    const uint16_t checksum = ipv6_udp_checksum(ip + 8, ip + 24, udp, UDP_HEADER_SIZE + NTP_PACKET_SIZE);
    udp[6] = static_cast<uint8_t>(checksum >> 8);
    udp[7] = static_cast<uint8_t>(checksum);

    esp_err_t result = ESP_ERR_INVALID_STATE;
    if (s_hardware_ntp_accepting.load(std::memory_order_acquire) && s_hardware_ntp_transmit_mutex != nullptr &&
        xSemaphoreTake(s_hardware_ntp_transmit_mutex, portMAX_DELAY) == pdTRUE)
    {
        if (s_hardware_ntp_accepting.load(std::memory_order_acquire))
        {
            for (uint32_t attempt = 0; attempt < HARDWARE_NTP_TRANSMIT_RETRY_COUNT; ++attempt)
            {
                if (!interleaved_reply)
                {
                    write_ntp_timestamp(reply, 40, get_current_time_in_ntp64_format());
                }
                size_t reply_length = NTP_PACKET_SIZE;
#if SYMMETRIC_KEY_AUTHENTICATION_ENABLED
                if (authenticated_request && !ntp_auth_append_response(reply, sizeof(reply), &reply_length, authentication_key_id))
                    break;
#endif
                ip[4] = static_cast<uint8_t>((UDP_HEADER_SIZE + reply_length) >> 8);
                ip[5] = static_cast<uint8_t>(UDP_HEADER_SIZE + reply_length);
                udp[4] = static_cast<uint8_t>((UDP_HEADER_SIZE + reply_length) >> 8);
                udp[5] = static_cast<uint8_t>(UDP_HEADER_SIZE + reply_length);
                memcpy(udp + UDP_HEADER_SIZE, reply, reply_length);
                udp[6] = 0;
                udp[7] = 0;
                const uint16_t refreshed_checksum = ipv6_udp_checksum(ip + 8, ip + 24, udp, UDP_HEADER_SIZE + reply_length);
                udp[6] = static_cast<uint8_t>(refreshed_checksum >> 8);
                udp[7] = static_cast<uint8_t>(refreshed_checksum);
                result = esp_eth_transmit(handle, response_frame, ETH_HEADER_SIZE + IPV6_HEADER_SIZE + UDP_HEADER_SIZE + reply_length);
                if (result != ESP_ERR_NO_MEM)
                    break;
                esp_rom_delay_us(HARDWARE_NTP_TRANSMIT_RETRY_DELAY_US);
            }
        }
        xSemaphoreGive(s_hardware_ntp_transmit_mutex);
    }
    if (result == ESP_OK)
    {
        ntp_cache_update_ipv6(&client_ip, client_port, receive_time, read_ntp_timestamp(reply, 40));
        const int64_t response_us = esp_timer_get_time();
        s_last_hardware_ntp_response_us.store(response_us, std::memory_order_release);
        s_last_ntp_response_us.store(response_us, std::memory_order_relaxed);
#if MQTT_ENABLED
        s_ntp_responses.fetch_add(1, std::memory_order_relaxed);
#endif
    }

    release_hardware_ntp_request_buffer(frame);
    return result;
}

static esp_err_t ntp_ethernet_input(esp_eth_handle_t handle, uint8_t *frame, uint32_t length, void *netif, void *info)
{
    if (s_ethernet_recovery_rx_probe_active.load(std::memory_order_relaxed))
        s_ethernet_recovery_rx_probe_frames.fetch_add(1, std::memory_order_relaxed);
    size_t ip_offset = 0;
    size_t udp_offset = 0;
    const eth_mac_time_t *rx_timestamp = static_cast<const eth_mac_time_t *>(info);
    const bool ipv4_request = is_ipv4_ntp_request(frame, length, &ip_offset, &udp_offset);
    const bool ipv6_request = !ipv4_request && is_ipv6_ntp_request(frame, length, &ip_offset, &udp_offset);
    if ((!ipv4_request && !ipv6_request) || (ipv4_request && !IPV4_ENABLED) || (ipv6_request && !IPV6_ENABLED))
        return esp_netif_receive(static_cast<esp_netif_t *>(netif), frame, length, nullptr);
    const uint8_t *request = frame + udp_offset + UDP_HEADER_SIZE;
    const uint8_t version = (request[0] >> 3) & 0x07;
    const uint8_t mode = request[0] & 0x07;
    if (version < 3 || version > 4 || mode != 3)
    {
        return esp_netif_receive(static_cast<esp_netif_t *>(netif), frame, length, nullptr);
    }

    bool internal_request = false;
    if (frame[12] == 0x08 && frame[13] == 0x00)
    {
        struct in_addr source_address{};
        memcpy(&source_address, frame + ip_offset + 12, sizeof(source_address));
        internal_request = is_internal_ntp_ipv4_address(source_address);
    }
    else
    {
        struct in6_addr source_address{};
        memcpy(&source_address, frame + ip_offset + 8, sizeof(source_address));
        internal_request = is_internal_ntp_ipv6_address(source_address);
    }
    if (!s_ntp_external_responses_enabled.load(std::memory_order_acquire) && !internal_request)
    {
        free(frame);
        return ESP_OK;
    }

    if (!timestamp_is_valid(rx_timestamp))
    {
        record_ntp_input(esp_timer_get_time());
        free(frame);
        return ESP_OK;
    }

#if MQTT_ENABLED
    s_ntp_requests_this_second.fetch_add(1, std::memory_order_relaxed);
#endif
    if (!admit_ntp_request())
    {
        free(frame);
        return ESP_OK;
    }
    const eth_mac_time_t receive_timestamp = *rx_timestamp;
    if (!s_hardware_ntp_accepting.load(std::memory_order_acquire) || s_hardware_ntp_request_queue == nullptr ||
        s_hardware_ntp_request_buffer_queue == nullptr)
    {
        free(frame);
    }
    else
    {
        uint8_t *request_buffer = nullptr;
        if (length > HARDWARE_NTP_REQUEST_BUFFER_SIZE ||
            xQueueReceive(s_hardware_ntp_request_buffer_queue, &request_buffer, 0) != pdTRUE)
        {
            free(frame);
            return ESP_OK;
        }
        memcpy(request_buffer, frame, length);
        free(frame);

        const hardware_ntp_request_t ntp_request{handle, request_buffer, length, static_cast<esp_netif_t *>(netif), receive_timestamp};
        if (xQueueSend(s_hardware_ntp_request_queue, &ntp_request, 0) != pdTRUE)
        {
            release_hardware_ntp_request_buffer(request_buffer);
        }
    }
    return ESP_OK;
}

static void ntp_cache_purge_task(void *parameter)
{
    (void)parameter;
    for (;;)
    {
        vTaskDelay(pdMS_TO_TICKS(60000));
        ntp_cache_purge_expired();

#if CALCULATE_STACK_SIZES_ENABLED
        report_current_task_stack_usage(NTP_Cache_Purge);
#endif
    }
}

// Handles NTP requests from IPv4 sources using Ethernet hardware timestamps to provide high-precision, GNSS-disciplined time responses.
// If the hardware timestamp is not available or valid, the request will be handled by the standard NTP server (ntp_server_task).
static void hardware_ntp_server_task(void *parameter)
{
    (void)parameter;
    hardware_ntp_request_t ntp_request{};
    for (;;)
    {
        if (xQueueReceive(s_hardware_ntp_request_queue, &ntp_request, portMAX_DELAY) == pdTRUE)
        {
            if (ntp_request.frame[12] == 0x86 && ntp_request.frame[13] == 0xDD && IPV6_ENABLED)
                process_hardware_ipv6_ntp_request(ntp_request.handle, ntp_request.frame, ntp_request.length,
                                                  ntp_request.netif, &ntp_request.rx_timestamp);
            else if (IPV4_ENABLED)
                process_hardware_ntp_request(ntp_request.handle, ntp_request.frame, ntp_request.length,
                                             ntp_request.netif, &ntp_request.rx_timestamp);
            else
                release_hardware_ntp_request_buffer(ntp_request.frame);
#if CALCULATE_STACK_SIZES_ENABLED
            report_current_task_stack_usage(Hardware_NTP_Server);
#endif
        }
    }
}

enum class ethernet_recovery_result_t : uint8_t
{
    recovered,
    retry_later,
    link_unavailable,
    no_ip,
    receive_unavailable,
    driver_failed,
    timestamp_failed
};

static bool physical_ethernet_link_is_up()
{
    const esp_eth_handle_t handle = ETH.handle();
    esp_eth_phy_t *phy = nullptr;
    if (handle == nullptr || esp_eth_get_phy_instance(handle, &phy) != ESP_OK || phy == nullptr || phy->get_link(phy) != ESP_OK)
        return false;

    return s_ethernet_connected.load(std::memory_order_acquire);
}

static ethernet_recovery_result_t restart_ethernet_transport()
{
    const esp_eth_handle_t handle = ETH.handle();
    if (handle == nullptr || s_hardware_ntp_transmit_mutex == nullptr ||
        !s_hardware_ntp_accepting.load(std::memory_order_acquire) ||
        xSemaphoreTake(s_hardware_ntp_transmit_mutex, pdMS_TO_TICKS(ETHERNET_RECOVERY_STOP_TIMEOUT_MS)) != pdTRUE)
        return ethernet_recovery_result_t::retry_later;

    s_ethernet_recovery_in_progress.store(true, std::memory_order_release);
    s_hardware_ntp_accepting.store(false, std::memory_order_release);
    esp_err_t result = esp_eth_stop(handle);
    xSemaphoreGive(s_hardware_ntp_transmit_mutex);
    if (result != ESP_OK)
    {
        s_hardware_ntp_accepting.store(true, std::memory_order_release);
        s_ethernet_recovery_in_progress.store(false, std::memory_order_release);
        return ethernet_recovery_result_t::driver_failed;
    }

    xEventGroupClearBits(s_net_event_group, ETH_CONNECTED_BIT | ETH_GOT_IP_BIT | ETH_GOT_IP6_BIT | ETH_GOT_ROUTABLE_IP6_BIT);
    vTaskDelay(pdMS_TO_TICKS(ETHERNET_RECOVERY_DELAY_MS));
    result = esp_eth_start(handle);
    if (result != ESP_OK)
    {
        s_ethernet_recovery_in_progress.store(false, std::memory_order_release);
        return ethernet_recovery_result_t::driver_failed;
    }

    esp_eth_mac_t *mac = nullptr;
    const eth_mac_ptp_config_t ptp_config = ETH_MAC_ESP_PTP_DEFAULT_CONFIG();
    s_ptp_clock_ready.store(false, std::memory_order_release);
    if (esp_eth_get_mac_instance(handle, &mac) != ESP_OK || mac == nullptr)
    {
        s_ethernet_recovery_in_progress.store(false, std::memory_order_release);
        return ethernet_recovery_result_t::timestamp_failed;
    }
    if (esp_eth_mac_ptp_enable(mac, &ptp_config) != ESP_OK ||
        esp_eth_mac_enable_ts4all(mac, true) != ESP_OK ||
        esp_eth_update_input_path_info(handle, ntp_ethernet_input, ETH.netif()) != ESP_OK)
    {
        s_ethernet_recovery_in_progress.store(false, std::memory_order_release);
        return ethernet_recovery_result_t::timestamp_failed;
    }

    struct timeval system_time{};
    gettimeofday(&system_time, nullptr);
    const struct timespec ptp_time{system_time.tv_sec, static_cast<long>(system_time.tv_usec) * 1000L};
    if (clock_settime(CLOCK_PTP_SYSTEM, &ptp_time) != 0)
    {
        s_ethernet_recovery_in_progress.store(false, std::memory_order_release);
        return ethernet_recovery_result_t::timestamp_failed;
    }

    eth_mac_time_t first_time{};
    eth_mac_time_t second_time{};
    const bool first_read_ok = esp_eth_mac_get_ptp_time(mac, &first_time) == ESP_OK;
    vTaskDelay(pdMS_TO_TICKS(ETHERNET_RECOVERY_DELAY_MS));
    if (!first_read_ok || esp_eth_mac_get_ptp_time(mac, &second_time) != ESP_OK ||
        (second_time.seconds < first_time.seconds ||
         (second_time.seconds == first_time.seconds && second_time.nanoseconds <= first_time.nanoseconds)))
    {
        s_ethernet_recovery_in_progress.store(false, std::memory_order_release);
        return ethernet_recovery_result_t::timestamp_failed;
    }

    s_ptp_clock_ready.store(true, std::memory_order_release);
    s_hardware_ntp_accepting.store(true, std::memory_order_release);
    s_ethernet_recovery_rx_probe_frames.store(0, std::memory_order_relaxed);
    s_ethernet_recovery_rx_probe_active.store(true, std::memory_order_release);
    if ((xEventGroupWaitBits(s_net_event_group, ETH_CONNECTED_BIT, pdFALSE, pdFALSE,
                             pdMS_TO_TICKS(ETHERNET_RECOVERY_IP_TIMEOUT_MS)) &
         ETH_CONNECTED_BIT) == 0)
    {
        s_ethernet_recovery_rx_probe_active.store(false, std::memory_order_release);
        s_ethernet_recovery_in_progress.store(false, std::memory_order_release);
        return ethernet_recovery_result_t::link_unavailable;
    }
    const EventBits_t needed_ip = PreferIPvX == 1   ? ETH_GOT_IP_BIT
                                  : PreferIPvX == 2 ? ETH_GOT_ROUTABLE_IP6_BIT
                                  : PreferIPvX == 4 && s_ipv4_ever_acquired.load(std::memory_order_relaxed)
                                      ? ETH_GOT_IP_BIT
                                      : ETH_GOT_IP_BIT | ETH_GOT_IP6_BIT;
    const EventBits_t acquired_ip = xEventGroupWaitBits(s_net_event_group, needed_ip, pdFALSE, pdFALSE,
                                                        pdMS_TO_TICKS(ETHERNET_RECOVERY_IP_TIMEOUT_MS));
    const bool linked = s_ethernet_connected.load(std::memory_order_acquire);
    s_ethernet_recovery_rx_probe_active.store(false, std::memory_order_release);
    const uint32_t recovery_rx_frames = s_ethernet_recovery_rx_probe_frames.load(std::memory_order_relaxed);
    s_ethernet_recovery_in_progress.store(false, std::memory_order_release);
    if (!linked)
    {
        s_last_physical_link_down_us.store(esp_timer_get_time(), std::memory_order_relaxed);
        return ethernet_recovery_result_t::link_unavailable;
    }
    if ((acquired_ip & needed_ip) == 0)
    {
        if (recovery_rx_frames == 0)
            return ethernet_recovery_result_t::receive_unavailable;
    }
    return (acquired_ip & needed_ip) != 0 ? ethernet_recovery_result_t::recovered : ethernet_recovery_result_t::no_ip;
}
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
extern "C" void app_main()
{

    setup_pps_input(); // (keep this at the very beginning of the setup sequence)

    initArduino();

    write_opening_messages_to_the_console();

    setup_mqtt_tf_queue();

    setup_NVS_storage();

    setup_mutexes_and_semaphores();

    setup_the_RGB_LED();

    setup_the_LCD();

    setup_the_button();

    start_RGB_LED_LCD_and_Button_refresh();

    const bool ethernet_setup_started = start_ethernet_setup_task(xTaskGetCurrentTaskHandle());

    setup_the_gnss();

    if (ethernet_setup_started)
        ulTaskNotifyTake(pdTRUE, portMAX_DELAY);

    setup_for_ote_updates();

    setup_mqtt();

    setup_symmetric_key_authentication();

    setup_ntp_server();

    setup_recovery_task();

    perform_health_check();

    write_open_for_business_messages_to_the_console();
}
